MUNAKATA-EPC/Artemis_2023/Tournaments/2023_01_RoboChallenge/PresentationSeat/Pictures/Robo2.png

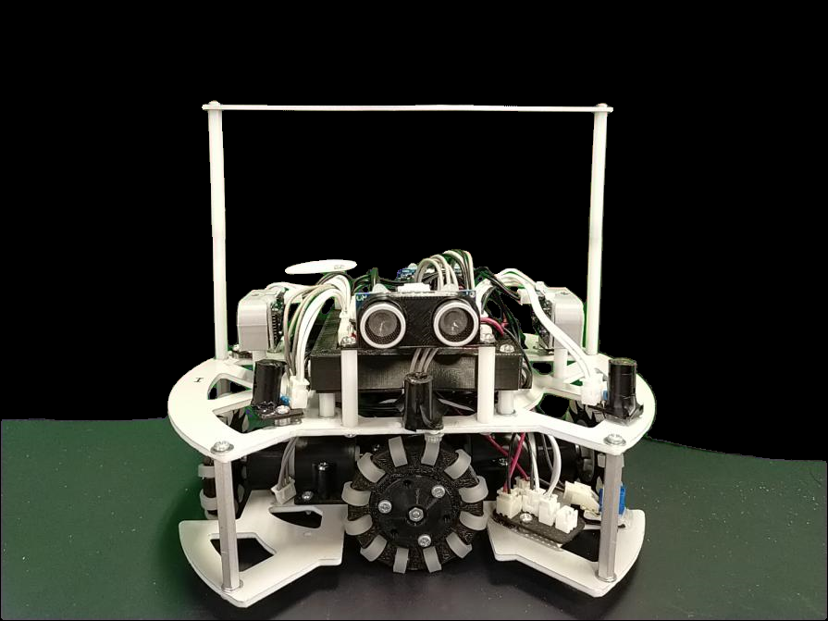
Tournaments/2023_01_RoboChallenge/PresentationSeat/Pictures/Robo2.png
