MUNAKATA-EPC/Artemis_2023/Design/2022 early/screw nut spacer/10mmスペーサー .png

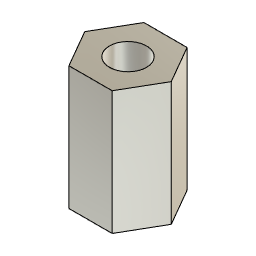
Design/2022 early/screw nut spacer/10mmスペーサー .png
