MUNAKATA-EPC/Artemis_2023/Design/2022 early/screw nut spacer/キャップボルト 8mm .png

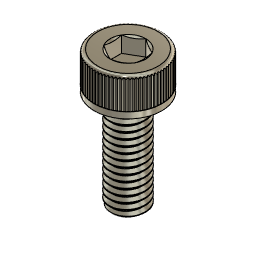
Design/2022 early/screw nut spacer/キャップボルト 8mm .png
