MUNAKATA-EPC/Artemis_2023/Design/artemis_pic/artemis.png

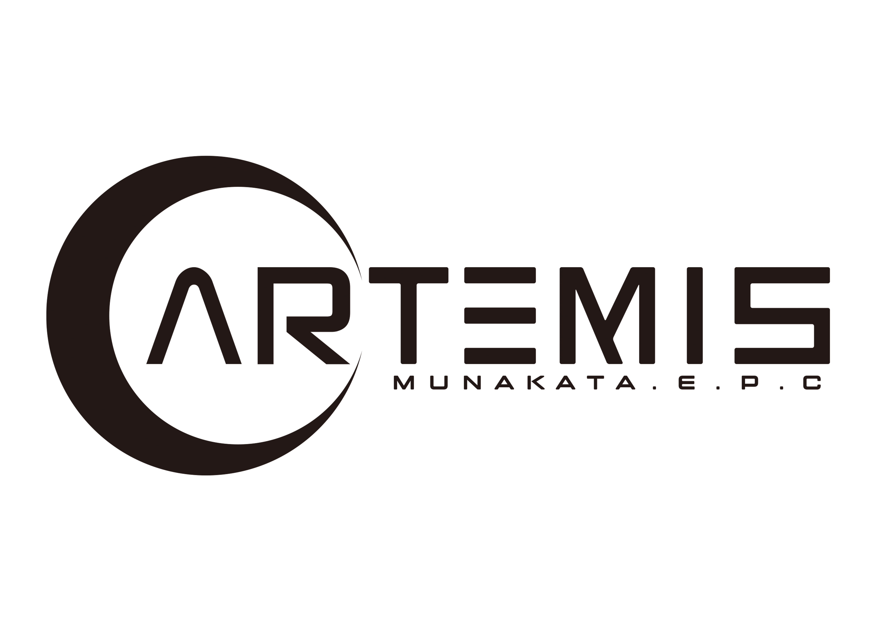
Design/artemis_pic/artemis.png
