MUNAKATA-EPC/Artemis_2023/Design/artemis_pic/artemis_text3.png

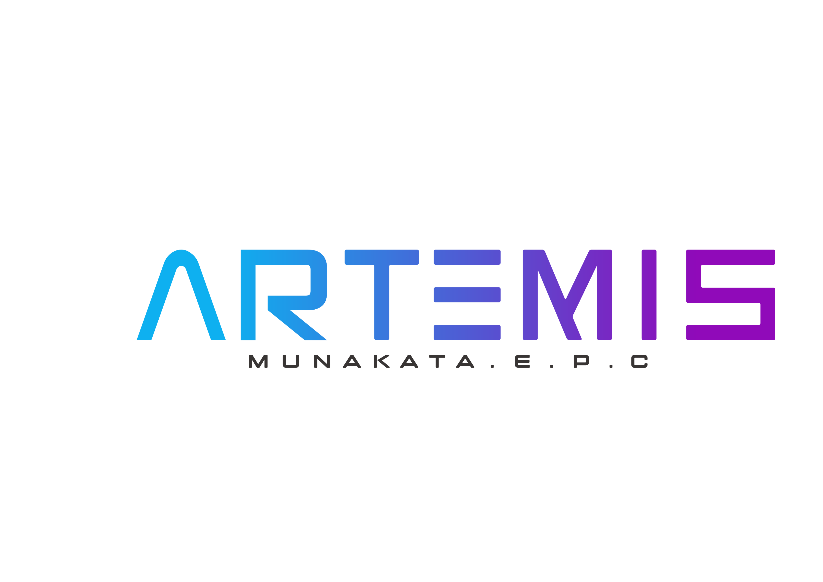
Design/artemis_pic/artemis_text3.png
