MUNAKATA-EPC/Artemis_2023/Design/artemis_pic/artemis_text.png

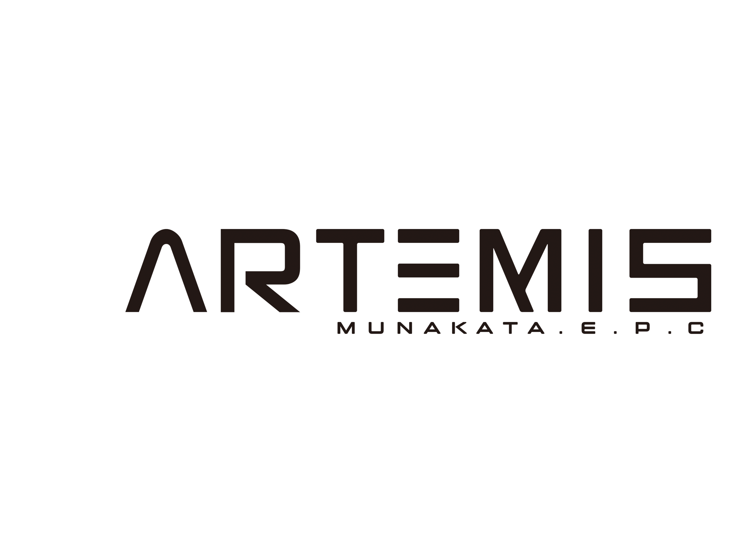
Design/artemis_pic/artemis_text.png
