MUNAKATA-EPC/Artemis_2023/Design/artemis_pic/moon2.png

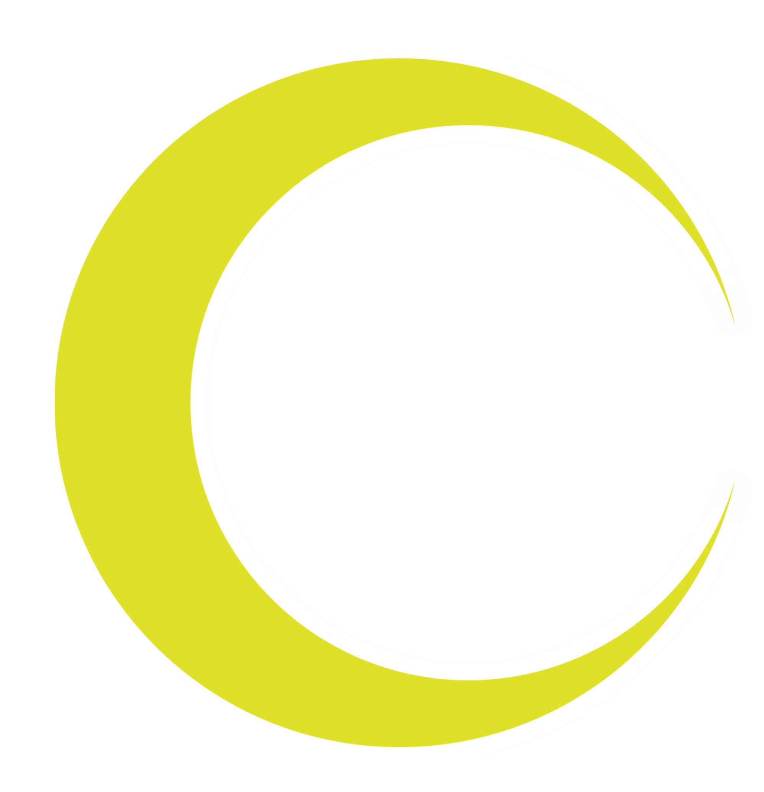
Design/artemis_pic/moon2.png
