MUNAKATA-EPC/Artemis_2023/Design/artemis_pic/moon_w.png

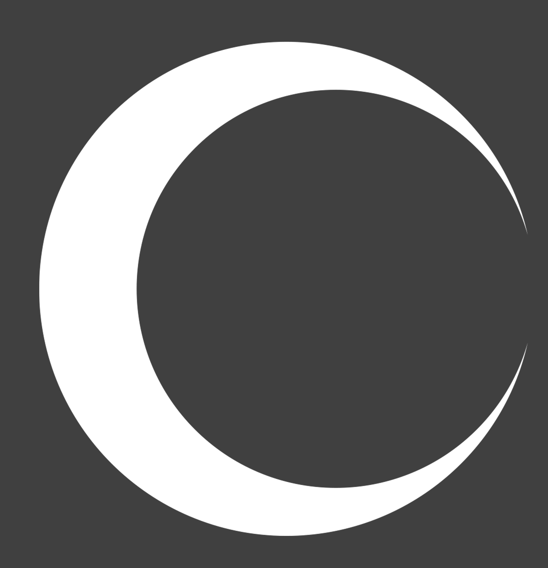
Design/artemis_pic/moon_w.png
