MUNAKATA-EPC/Artemis_2023/Tournaments/2023_00_KitakyusyuOpen/PresentationSeat/Pictures/JMP-BE-3561.png

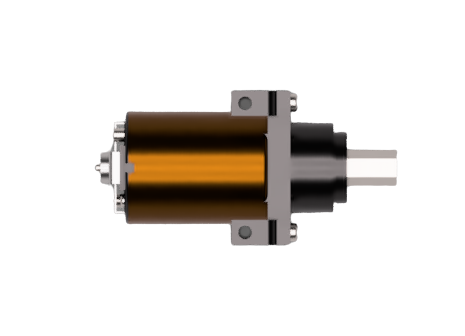
Tournaments/2023_00_KitakyusyuOpen/PresentationSeat/Pictures/JMP-BE-3561.png
