MUNAKATA-EPC/Artemis_2023/Tournaments/2023_00_KitakyusyuOpen/PresentationSeat/Pictures/Li-Po Battery.png

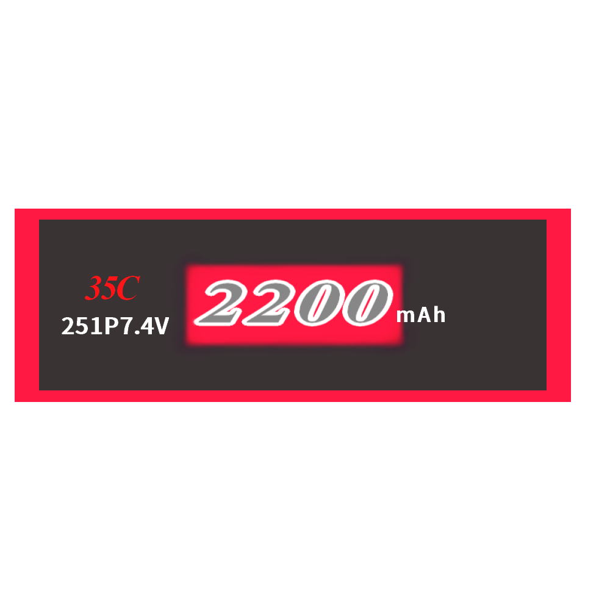
Tournaments/2023_00_KitakyusyuOpen/PresentationSeat/Pictures/Li-Po Battery.png
