MUNAKATA-EPC/Artemis_2023/Tournaments/2023_00_KitakyusyuOpen/PresentationSeat/Pictures/Motor.png

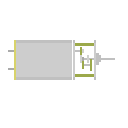
Tournaments/2023_00_KitakyusyuOpen/PresentationSeat/Pictures/Motor.png
