MUNAKATA-EPC/Artemis_2023/Tournaments/2023_00_KitakyusyuOpen/PresentationSeat/Pictures/Robo1.bmp

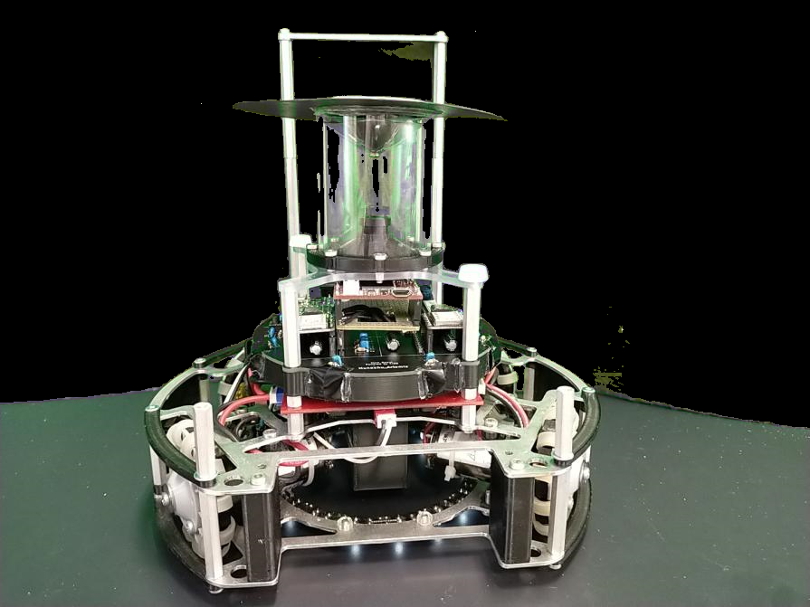
Tournaments/2023_00_KitakyusyuOpen/PresentationSeat/Pictures/Robo1.bmp
