MUNAKATA-EPC/Artemis_2023/Tournaments/2023_00_KitakyusyuOpen/PresentationSeat/Pictures/unknown.png

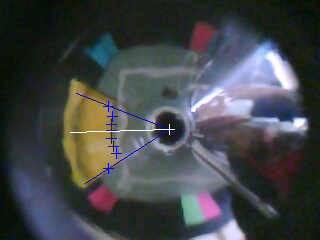
Tournaments/2023_00_KitakyusyuOpen/PresentationSeat/Pictures/unknown.png
