MUNAKATA-EPC/Artemis_2023/Tournaments/2023_04_JapanOpen/リチウムイオン二次電池資料/提出資料/WSL043_4.JPG

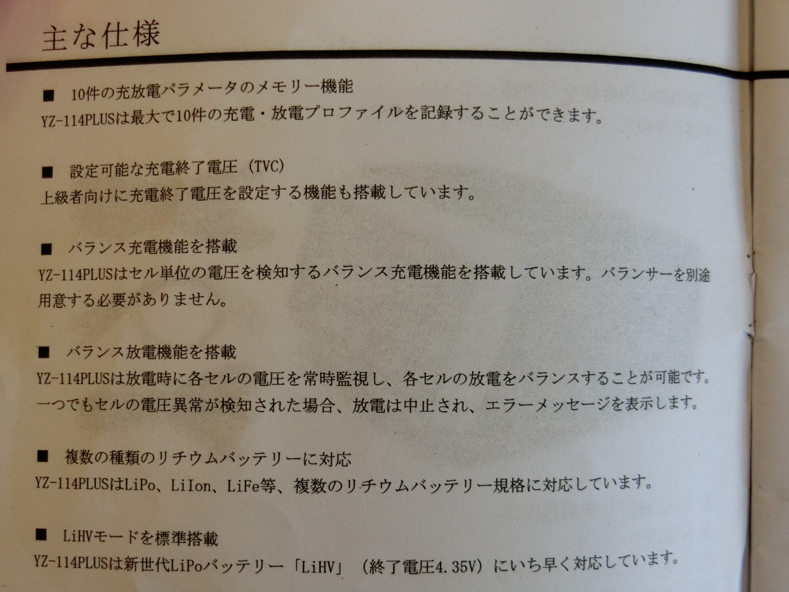
Tournaments/2023_04_JapanOpen/リチウムイオン二次電池資料/提出資料/WSL043_4.JPG
