MUNAKATA-EPC/Artemis_2023/Design/2022 late/ver.Teensy/3D printed components/筒固定具.stl

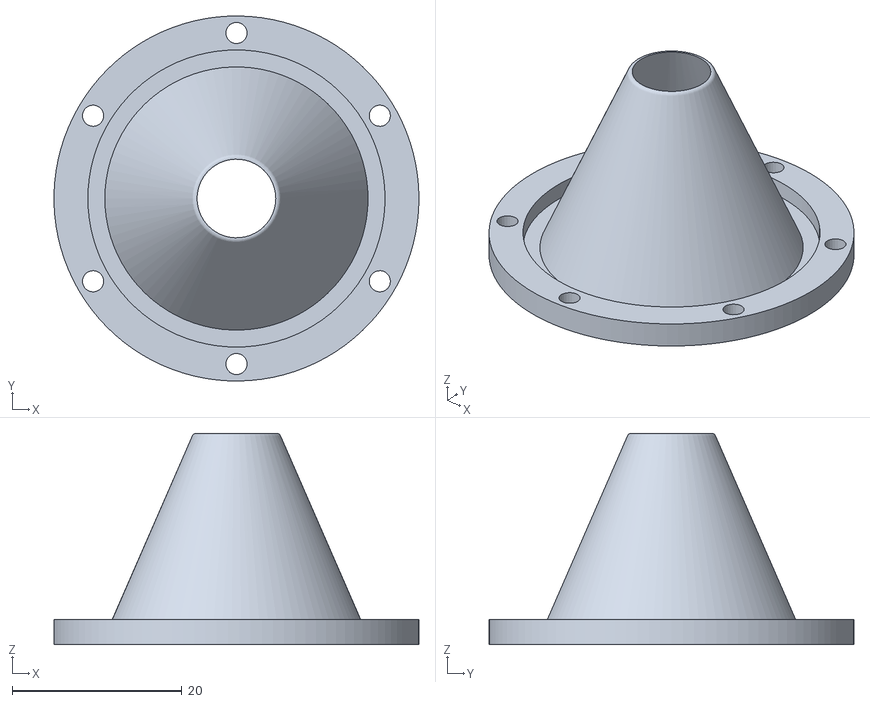
[picture p106: CAD file, 2022-12-09]
Design/2022 late/ver.Teensy/3D printed components/筒固定具.stl
43.0 x 43.0 x 24.9
