MUNAKATA-EPC/Artemis_2023/Design/2022 late/ver.Teensy/electric components/psu_board.step

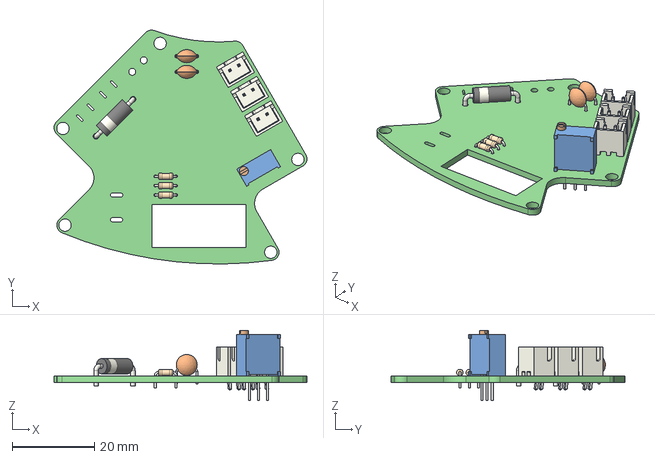
[picture p107: CAD file, 2022-12-09]
Design/2022 late/ver.Teensy/electric components/psu_board.step
61.5 x 56.9 x 17.1 mm
psu_board PCB
