MUNAKATA-EPC/Artemis_2023/Design/2022 late/ver.Teensy/jlcpcb_3dprinting/top_frame.stl

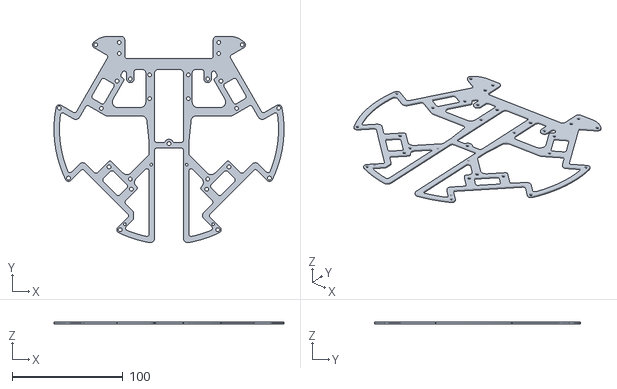
[picture p108: CAD file, 2022-12-09]
Design/2022 late/ver.Teensy/jlcpcb_3dprinting/top_frame.stl
207.9 x 186.5 x 1.50
