MUNAKATA-EPC/Artemis_2023/KiCad_Projects/3D_Data/2022 late/キッカー基板 v1.dxf

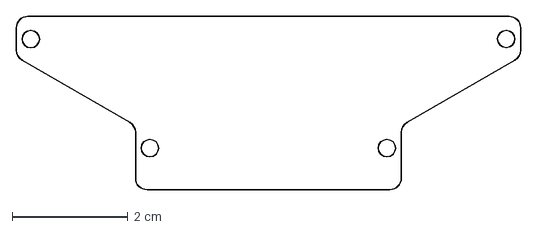
[picture p109: CAD file, 2022-12-09]
KiCad_Projects/3D_Data/2022 late/キッカー基板 v1.dxf
8.73 x 3.00 cm
