MUNAKATA-EPC/Artemis_2023/KiCad_Projects/3D_Data/2023 early/line統合.dxf

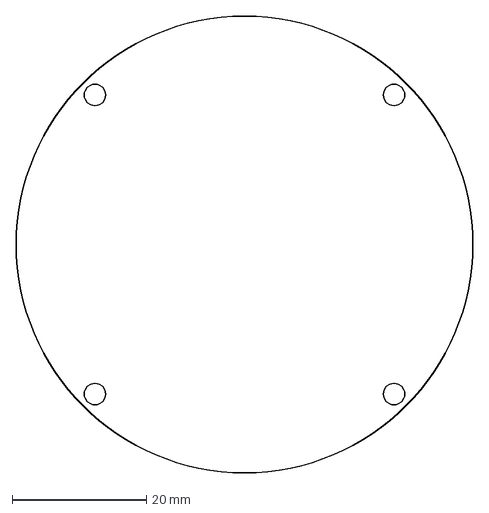
[picture p110: CAD file, 2023-03-06]
KiCad_Projects/3D_Data/2023 early/line統合.dxf
68.0 x 68.0 mm
