MUNAKATA-EPC/Artemis_2023/KiCad_Projects/3D_Data/ラインセンサー基板 .dxf

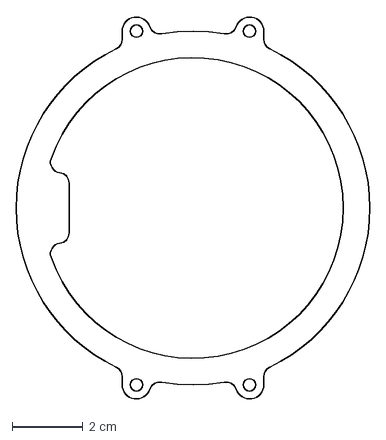
[picture p111: CAD file, 2022-06-29]
KiCad_Projects/3D_Data/ラインセンサー基板 .dxf
10.0 x 10.9 cm
