MUNAKATA-EPC/Artemis_2023/Design/2022 early/3D printed components/筒固定具.stl

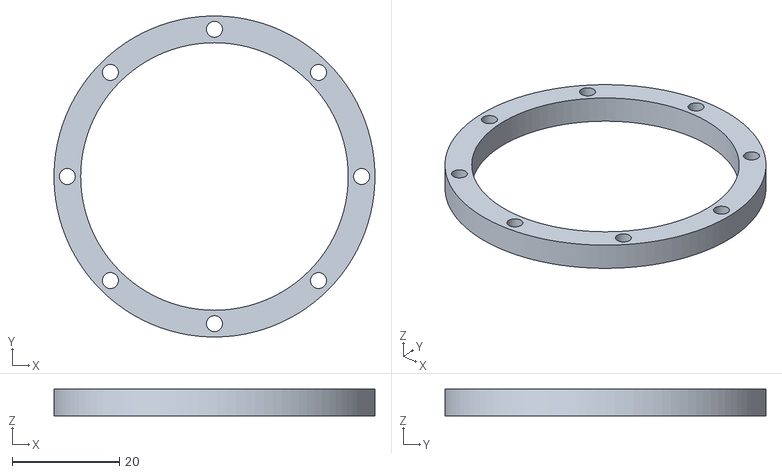
[picture p112: CAD file, 2022-07-31]
Design/2022 early/3D printed components/筒固定具.stl
60.0 x 60.0 x 5.00
