MUNAKATA-EPC/Artemis_2023/Design/2022 late/ver.Teensy/3D printed components/バッテリー固定具.stl

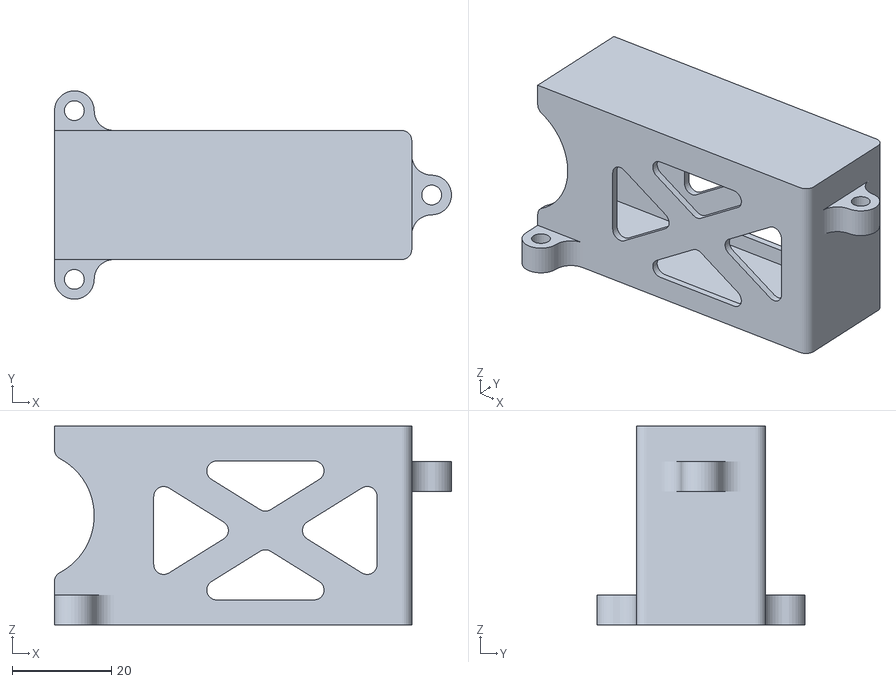
[picture p113: CAD file, 2022-12-09]
Design/2022 late/ver.Teensy/3D printed components/バッテリー固定具.stl
80.0 x 42.0 x 40.0
