MUNAKATA-EPC/Artemis_2023/Design/2022 late/ver.Teensy/electric components/kikker_PSU.step

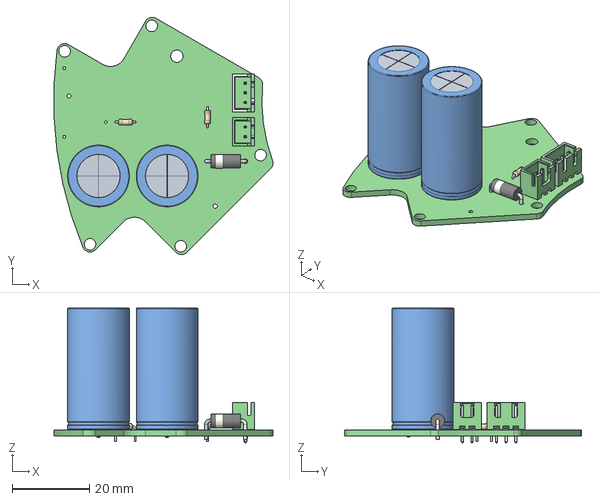
[picture p114: CAD file, 2022-12-09]
Design/2022 late/ver.Teensy/electric components/kikker_PSU.step
56.8 x 61.5 x 34.9 mm
kikker_PSU PCB
