MUNAKATA-EPC/Artemis_2023/Design/2022 late/ver.Teensy/jlcpcb_3dprinting/lower_frame.stl

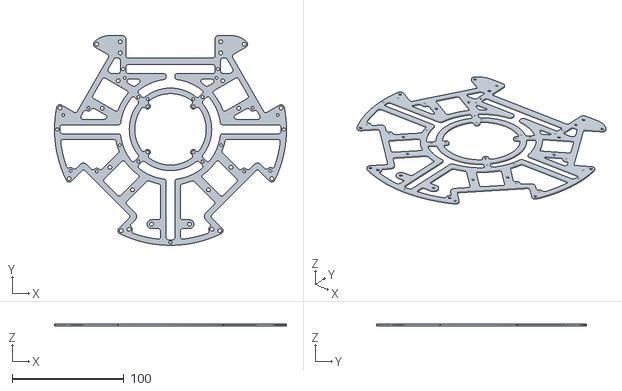
[picture p115: CAD file, 2022-12-09]
Design/2022 late/ver.Teensy/jlcpcb_3dprinting/lower_frame.stl
207.9 x 188.0 x 1.50
