MUNAKATA-EPC/Artemis_2023/KiCad_Projects/3D_Data/2022 late/IO基板 v4.dxf

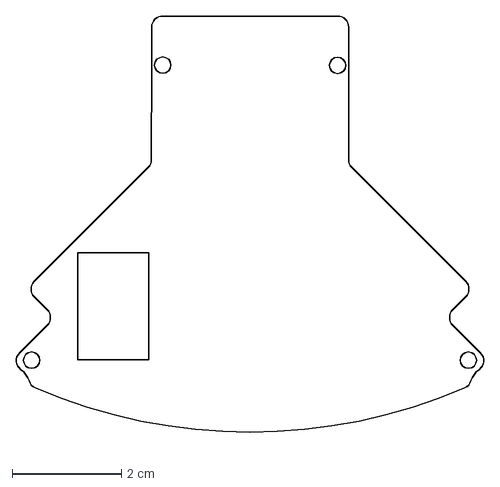
[picture p116: CAD file, 2022-10-13]
KiCad_Projects/3D_Data/2022 late/IO基板 v4.dxf
8.55 x 7.87 cm
