MUNAKATA-EPC/Artemis_2023/KiCad_Projects/3D_Data/IO基板 v1.dxf

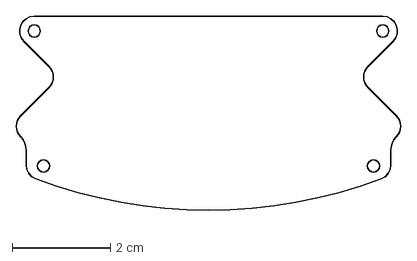
[picture p117: CAD file, 2022-06-24]
KiCad_Projects/3D_Data/IO基板 v1.dxf
7.84 x 4.17 cm
