MUNAKATA-EPC/Artemis_2023/Design/2022 early/3D printed components/バッテリーケース.stl

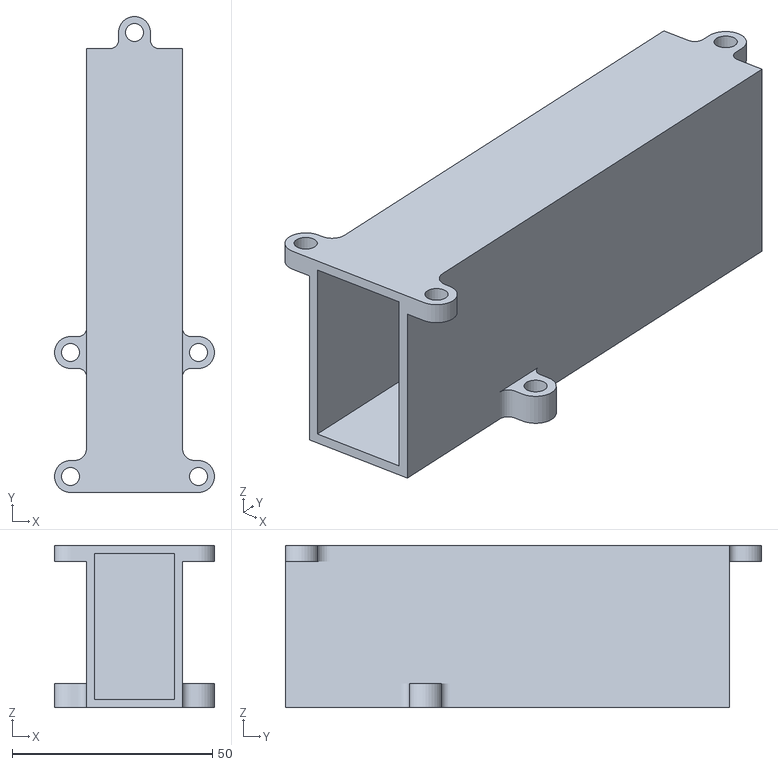
[picture p118: CAD file, 2022-07-31]
Design/2022 early/3D printed components/バッテリーケース.stl
40.0 x 119.0 x 40.5
