MUNAKATA-EPC/Artemis_2023/Design/2022 late/ver.Teensy/3D printed components/IR隠し.stl

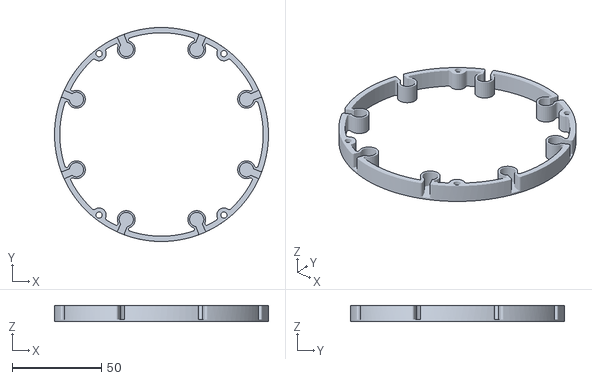
[picture p119: CAD file, 2022-12-09]
Design/2022 late/ver.Teensy/3D printed components/IR隠し.stl
120.0 x 120.0 x 9.00
