MUNAKATA-EPC/Artemis_2023/Design/2022 late/ver.Teensy/electric components/line 統合.step

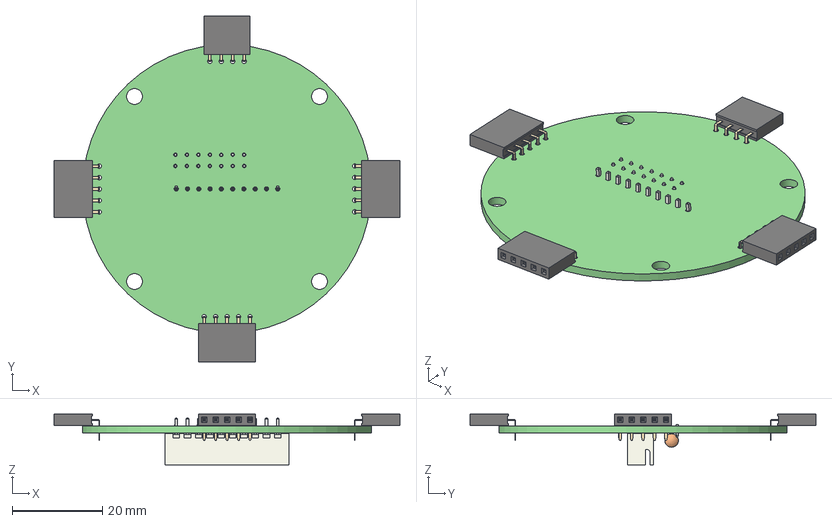
[picture p120: CAD file, 2022-10-13]
Design/2022 late/ver.Teensy/electric components/line 統合.step
76.7 x 76.7 x 11.2 mm
line çµ±å PCB
