MUNAKATA-EPC/Artemis_2023/Design/2022 early/3D printed components/IR隠し.stl

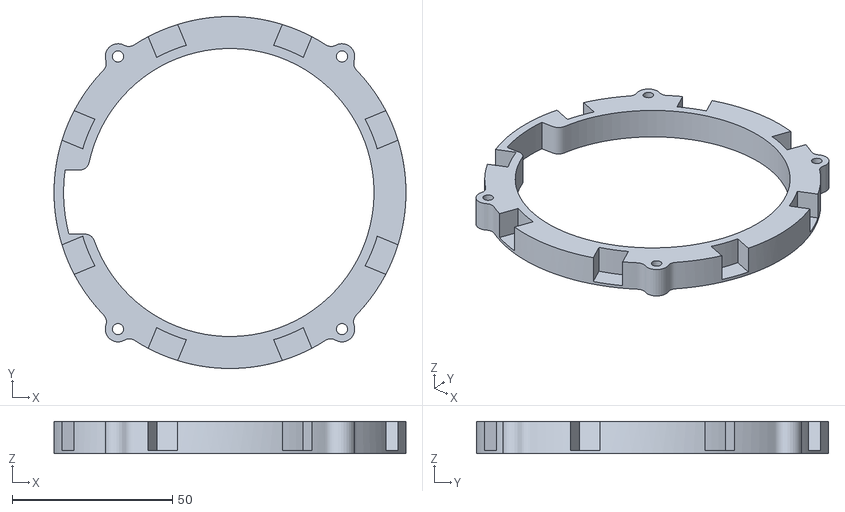
[picture p121: CAD file, 2022-07-31]
Design/2022 early/3D printed components/IR隠し.stl
110.0 x 110.0 x 10.0
