MUNAKATA-EPC/Artemis_2023/Design/2022 late/ver.Teensy/3D printed components/タッチセンサー v2.stl

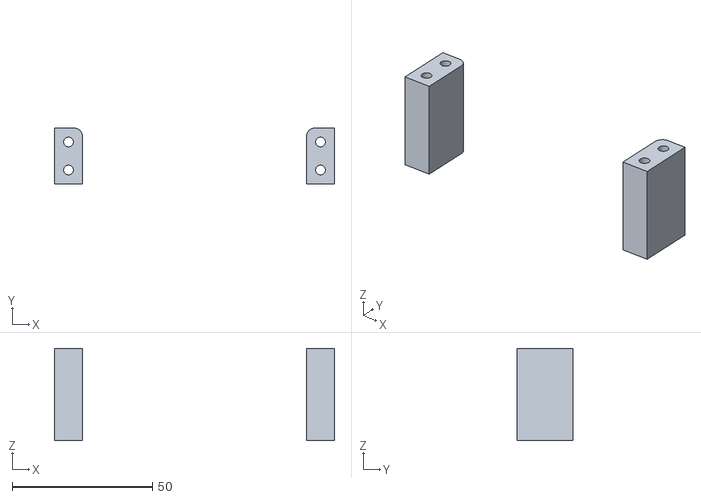
[picture p122: CAD file, 2022-12-09]
Design/2022 late/ver.Teensy/3D printed components/タッチセンサー v2.stl
100.0 x 20.0 x 33.0
