MUNAKATA-EPC/Artemis_2023/Design/2022 late/ver.Teensy/electric components/teensy4_header_breakout.step

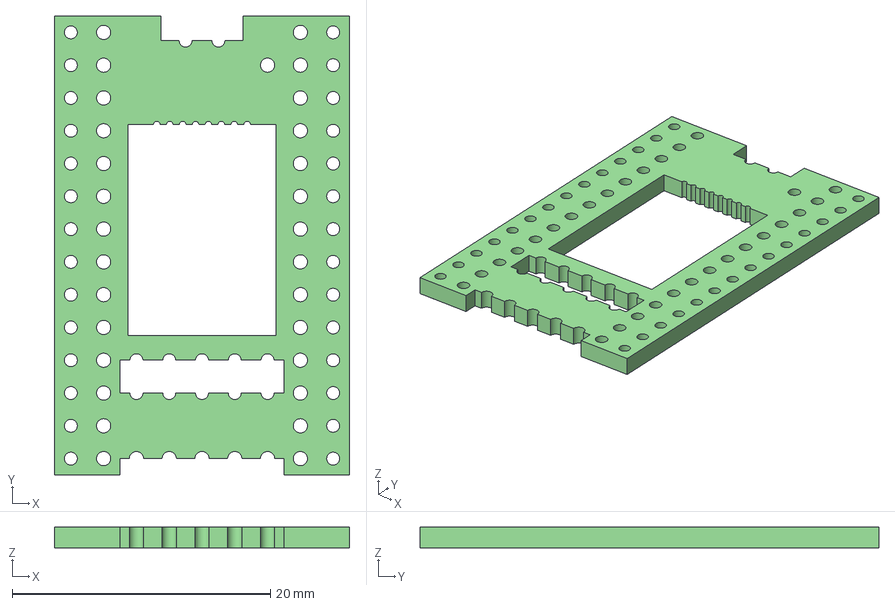
[picture p123: CAD file, 2022-10-13]
Design/2022 late/ver.Teensy/electric components/teensy4_header_breakout.step
22.9 x 35.6 x 1.60 mm
