MUNAKATA-EPC/Artemis_2023/Design/2022 late/ver.Teensy/jlcpcb_3dprinting/kikker_stay.stl

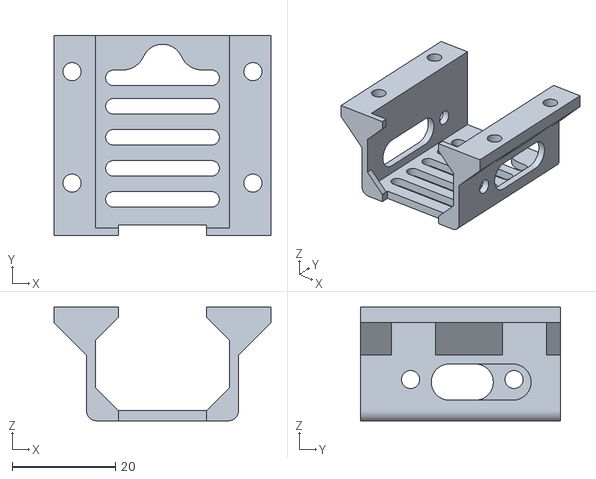
[picture p124: CAD file, 2022-12-09]
Design/2022 late/ver.Teensy/jlcpcb_3dprinting/kikker_stay.stl
42.0 x 38.7 x 22.0
