MUNAKATA-EPC/Artemis_2023/KiCad_Projects/3D_Data/2022 late/line統合.dxf

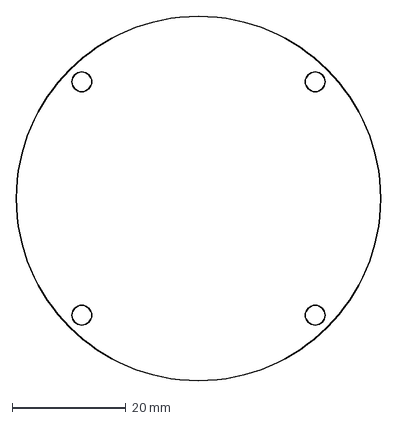
[picture p125: CAD file, 2022-10-13]
KiCad_Projects/3D_Data/2022 late/line統合.dxf
64.0 x 64.0 mm
