MUNAKATA-EPC/Artemis_2023/KiCad_Projects/3D_Data/基板 右 v3.dxf

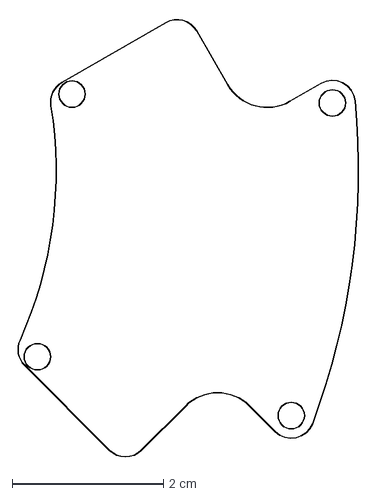
[picture p126: CAD file, 2022-06-22]
KiCad_Projects/3D_Data/基板 右 v3.dxf
4.62 x 5.83 cm
