MUNAKATA-EPC/Artemis_2023/Design/2022 late/ver.Teensy/3D printed components/5mm スペーサー v2.stl

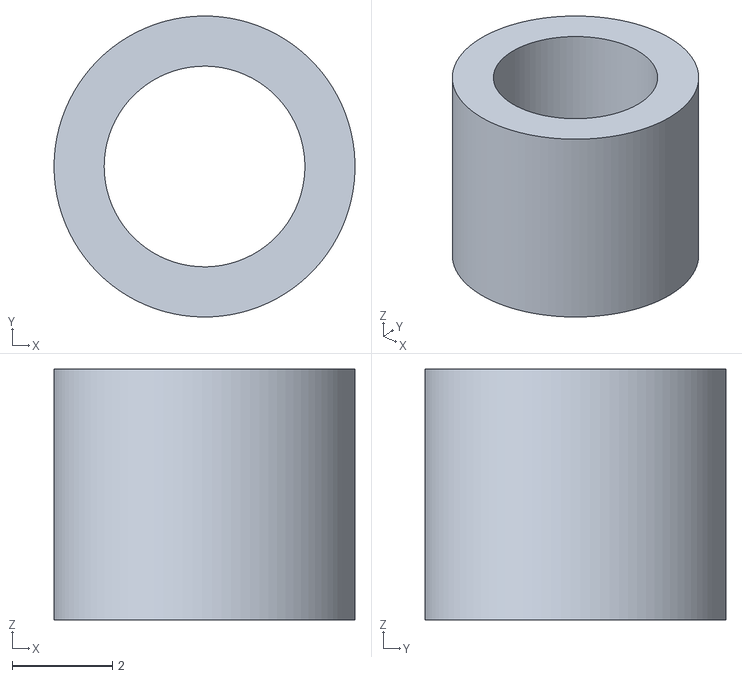
[picture p127: CAD file, 2022-12-09]
Design/2022 late/ver.Teensy/3D printed components/5mm スペーサー v2.stl
6.00 x 6.00 x 5.00
