MUNAKATA-EPC/Artemis_2023/Design/2022 late/ver.Teensy/electric components/line_sensor_right.step

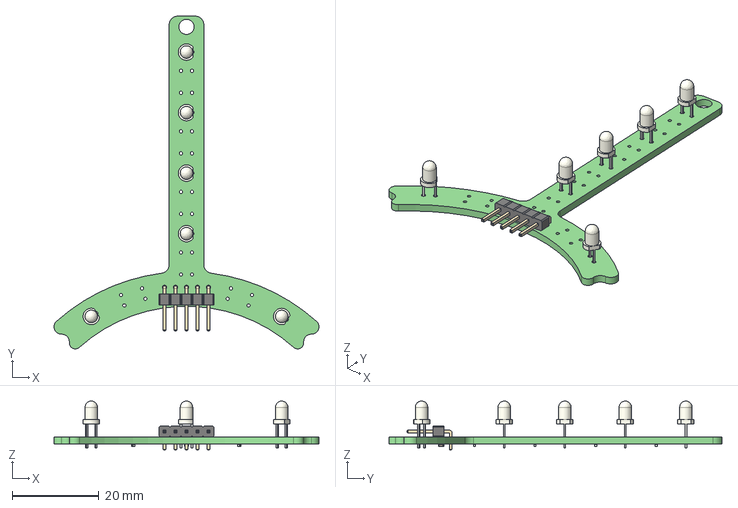
[picture p128: CAD file, 2022-10-13]
Design/2022 late/ver.Teensy/electric components/line_sensor_right.step
61.2 x 76.8 x 11.3 mm
line_sensor_right PCB
