MUNAKATA-EPC/Artemis_2023/Design/2022 late/ver.Teensy/jlcpcb_3dprinting/omni top.stl

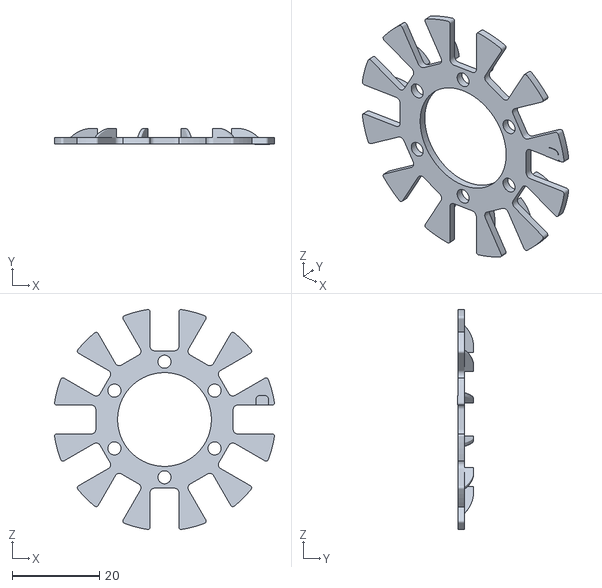
[picture p129: CAD file, 2022-07-31]
Design/2022 late/ver.Teensy/jlcpcb_3dprinting/omni top.stl
50.4 x 3.74 x 50.4
