MUNAKATA-EPC/Artemis_2023/KiCad_Projects/3D_Data/2022 late/ラインセンサー右.dxf

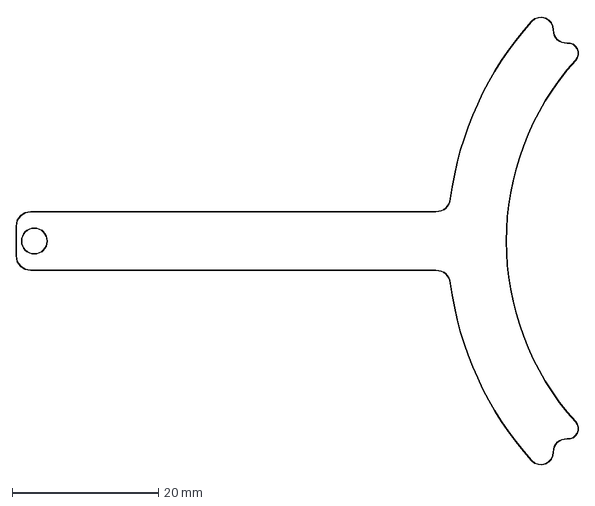
[picture p130: CAD file, 2022-10-13]
KiCad_Projects/3D_Data/2022 late/ラインセンサー右.dxf
76.9 x 61.4 mm
