MUNAKATA-EPC/Artemis_2023/Design/2022 late/ver.Teensy/electric components/line_sensor_front.step

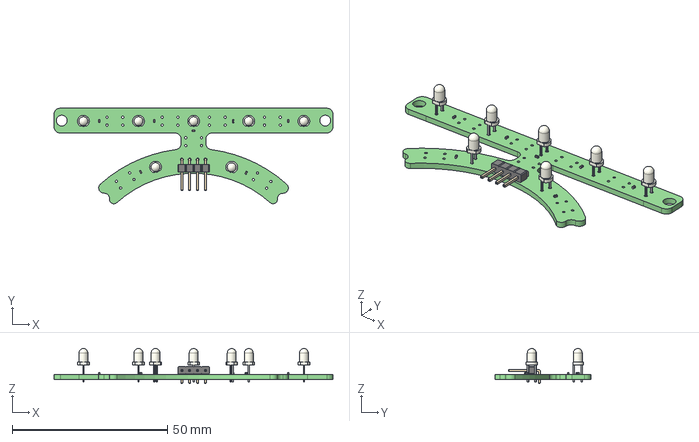
[picture p131: CAD file, 2022-10-13]
Design/2022 late/ver.Teensy/electric components/line_sensor_front.step
90.0 x 30.8 x 11.3 mm
line_sensor_front PCB
