MUNAKATA-EPC/Artemis_2023/Design/2022 late/ver.Teensy/jlcpcb_3dprinting/omuni stay.stl

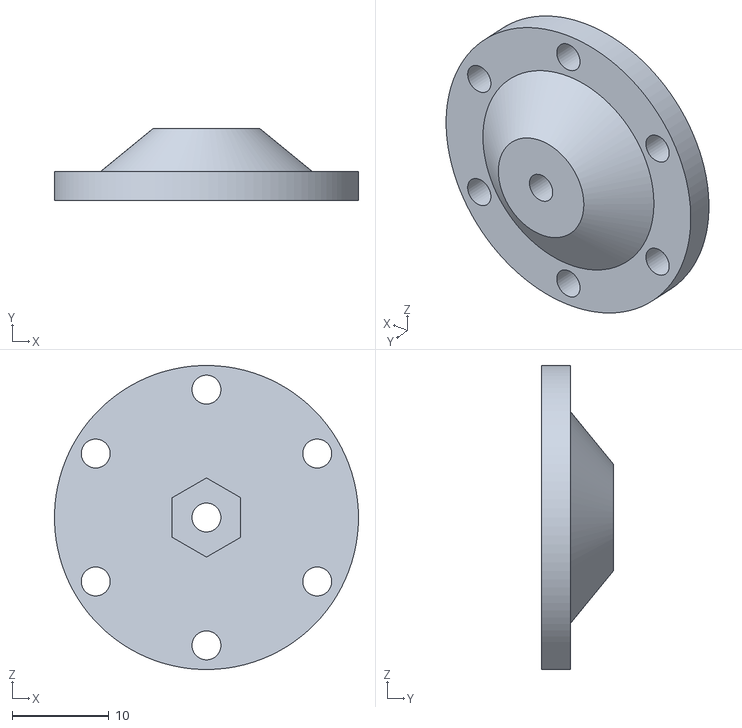
[picture p132: CAD file, 2022-06-01]
Design/2022 late/ver.Teensy/jlcpcb_3dprinting/omuni stay.stl
31.5 x 7.50 x 31.5
