MUNAKATA-EPC/Artemis_2023/KiCad_Projects/3D_Data/2022 late/基板左.dxf

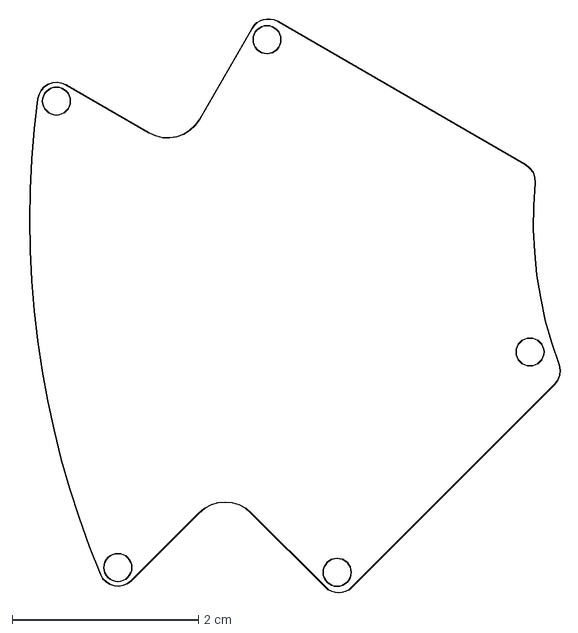
[picture p133: CAD file, 2022-10-13]
KiCad_Projects/3D_Data/2022 late/基板左.dxf
5.85 x 6.18 cm
