MUNAKATA-EPC/Artemis_2023/Design/2022 late/ver.Teensy/electric components/IO_Board.step

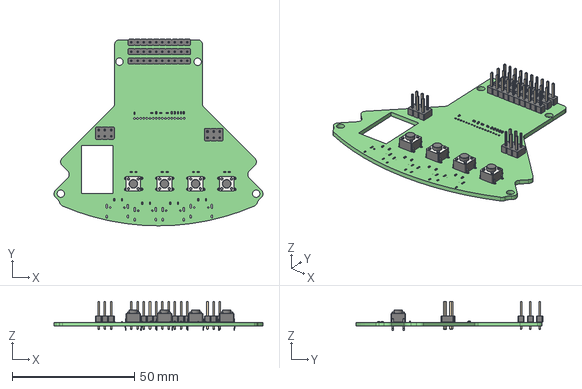
[picture p134: CAD file, 2022-10-13]
Design/2022 late/ver.Teensy/electric components/IO_Board.step
85.4 x 76.2 x 12.0 mm
IO_Board PCB
