MUNAKATA-EPC/Artemis_2023/Design/2022 late/ver.Teensy/jlcpcb_3dprinting/omni  lower.stl

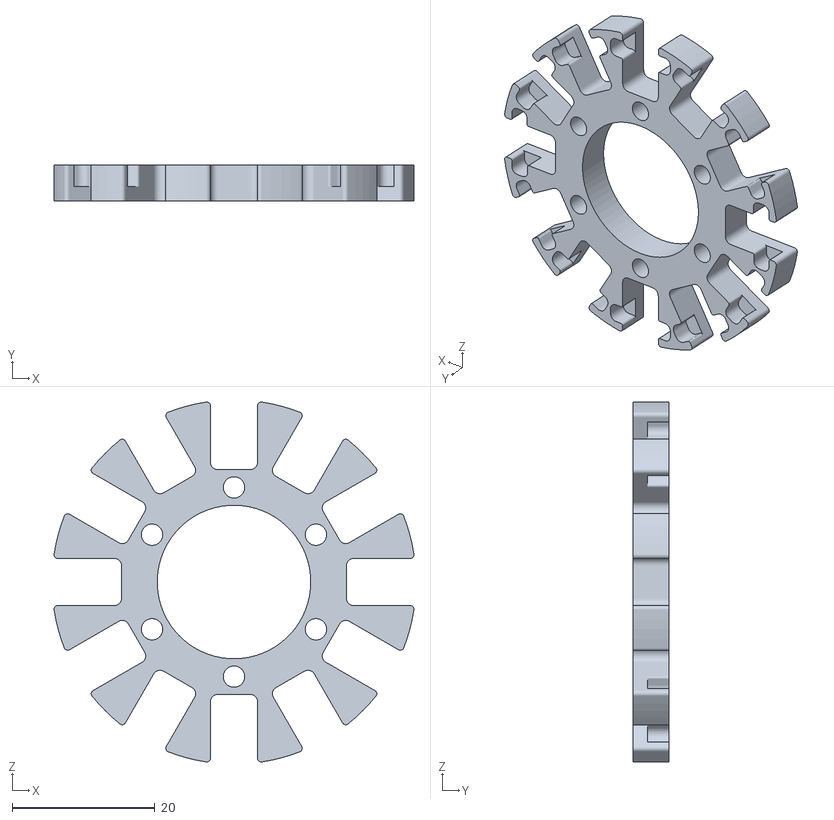
[picture p135: CAD file, 2022-06-01]
Design/2022 late/ver.Teensy/jlcpcb_3dprinting/omni lower.stl
50.4 x 5.00 x 50.4
