MUNAKATA-EPC/Artemis_2023/KiCad_Projects/3D_Data/2022 late/メイン基板 .dxf

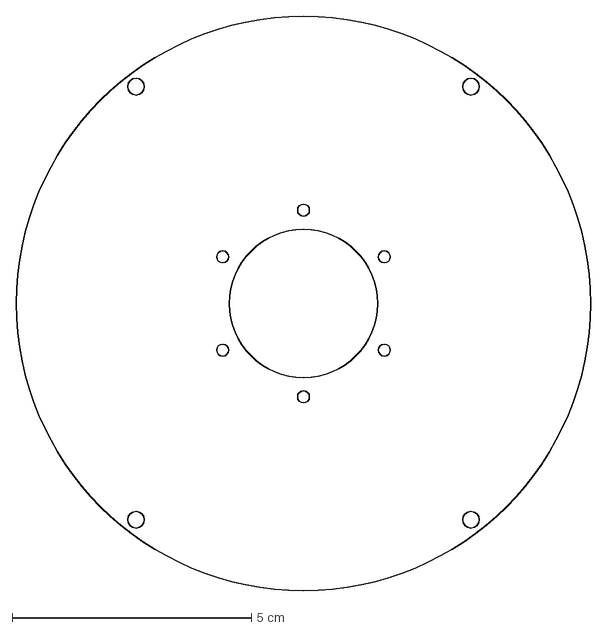
[picture p136: CAD file, 2022-10-13]
KiCad_Projects/3D_Data/2022 late/メイン基板 .dxf
12.0 x 12.0 cm
