MUNAKATA-EPC/Artemis_2023/KiCad_Projects/3D_Data/2022 late/ラインセンサー前 v1.dxf

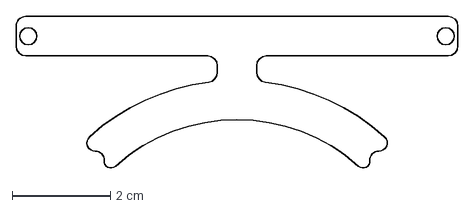
[picture p137: CAD file, 2022-10-13]
KiCad_Projects/3D_Data/2022 late/ラインセンサー前 v1.dxf
9.00 x 3.10 cm
