MUNAKATA-EPC/Artemis_2023/KiCad_Projects/その他/teensy4_header_breakout-master/teensy4_header_breakout-master/teensy4_header_breakout.kicad_pcb

## KiCad design KiCad_Projects/その他/teensy4_header_breakout-master/teensy4_header_breakout-master/teensy4_header_breakout.kicad_pcb (2022-10-13)

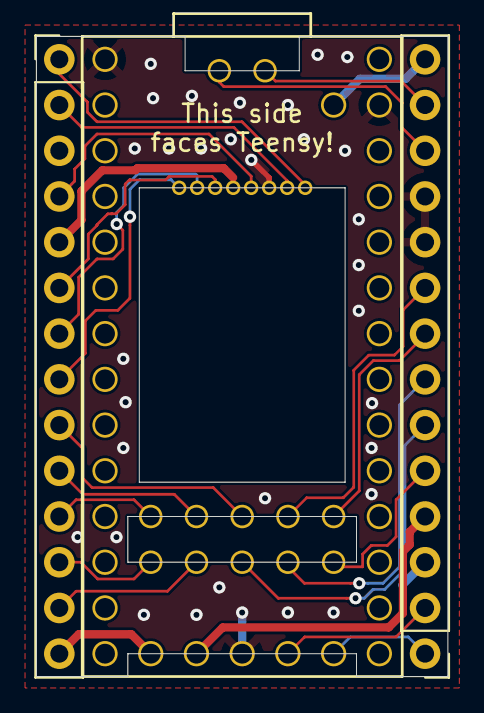
[picture p154: board teensy4_header_breakout.kicad_pcb from above]

Board: 2 copper layers, 22.9 x 35.6 mm, 3 parts (0 on the bottom side), 25 nets.

Parts:
J1, J2: Conn_01x14; PinHeader_1x14_P2.54mm_Vertical
U1: GND-1; Teensy40_SMT

Connections:
/3V3-1: J2.4, U1.16
/3V3-SD: J1.5, U1.49
/24: J2.5, U1.35
/25: J2.8, U1.36
/26: J2.7, U1.37
/27: J2.9, U1.38
/28: J2.6, U1.39
/29: J1.9, U1.40
/30: J1.13, U1.41
/31: J1.10, U1.42
/32: J1.12, U1.43
/33: J1.11, U1.44
/CLK: J1.4, U1.48
/CMD: J1.6, U1.50
/D+: J2.12, U1.54
/D-: J2.13, U1.53
/DAT0: J1.2, U1.46
/DAT1: J1.1, U1.45
/DAT2: J1.8, U1.52
/DAT3: J1.7, U1.51
/GND: J1.3, J2.3, J2.10, J2.11, U1.1, U1.17, U1.32, U1.47
/ON_OFF: J2.1, U1.19
/PROGRAM: J2.2, U1.18
/VBAT: J1.14, U1.15
/VUSB: J2.14, U1.34
