MUNAKATA-EPC/Artemis_2023/KiCad_Projects/2022 late/TJ3B_ver/main_board_TJ3B/main_board_TJ3B/main_board_TJ3B.kicad_pcb

## KiCad design KiCad_Projects/2022 late/TJ3B_ver/main_board_TJ3B/main_board_TJ3B/main_board_TJ3B.kicad_pcb (2023-03-06)

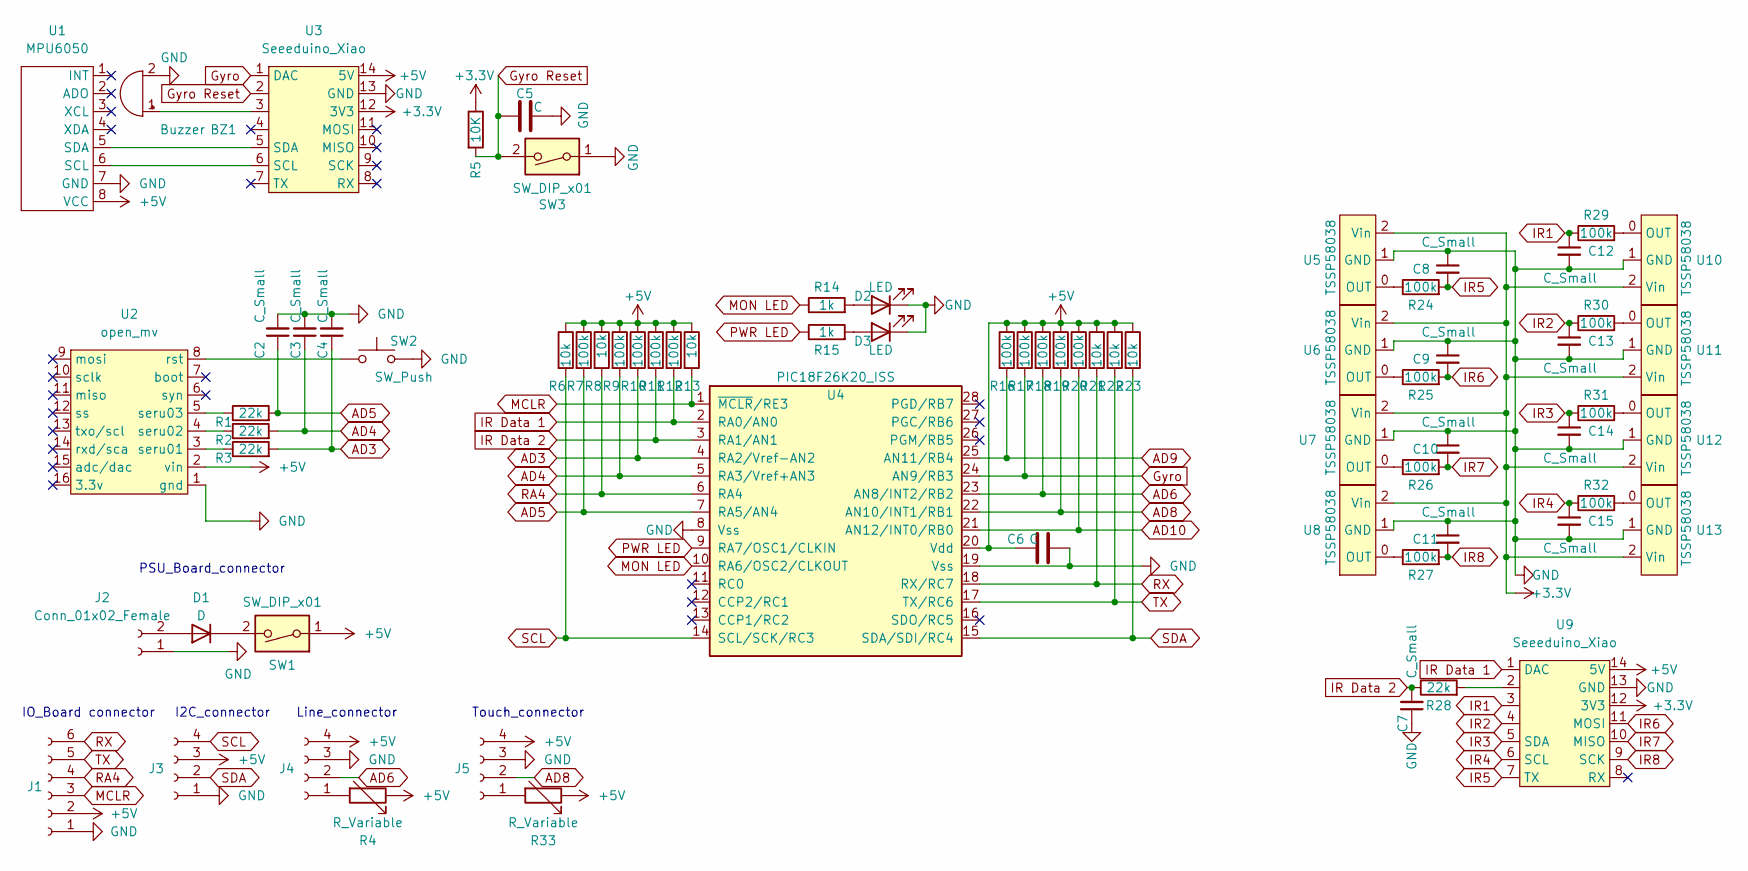
[picture p155: schematic main_board_TJ3B.kicad_sch]

Parts:
BZ1: Buzzer; Buzzer_12x9.5RM7.6
C2, C3, C4, C7: C_Small; C_0402_1005Metric; LCSC C528972
C5: C; C_0402_1005Metric; LCSC C507422
C6: C; CP_Radial_D5.0mm_P2.50mm
C8, C9, C10, C11, C12, C13, C14, C15: C_Small; C_0402_1005Metric; LCSC C507422
D1: D; D_DO-41_SOD81_P7.62mm_Horizontal
D2, D3: LED; LED_0402_1005Metric; LCSC C130725
J1: Conn_01x06_Female; JST_XH_B6B-XH-A_1x06_P2.50mm_Vertical
J2: Conn_01x02_Female; JST_XH_B2B-XH-A_1x02_P2.50mm_Vertical
J3, J4, J5: Conn_01x04_Female; JST_XH_B4B-XH-A_1x04_P2.50mm_Vertical
R1, R2, R3, R28: 22k; R_0402_1005Metric; LCSC C25768
R4, R33: R_Variable; 可変抵抗(小)
R5: 10K; R_0402_1005Metric; LCSC C269674
R6, R8, R13, R21, R22, R23: 10k; R_0402_1005Metric; LCSC C269674
R7, R9, R10, R11, R12, R16, R17, R18, R19, R20, R24, R25, R26, R27, R29, R30, R31, R32: 100k; R_0402_1005Metric; LCSC C269673
R14, R15: 1k; R_0402_1005Metric; LCSC C11702
SW1: SW_DIP_x01; 2MS1T2B4M2QES
SW2: SW_Push; SW_PUSH_6mm_H5mm
SW3: SW_DIP_x01; SW_PUSH_6mm_H5mm
U1: MPU6050
U2: open_mv; OpenMV
U3, U9: Seeeduino_Xiao; seeeduinoXIAO
U4: PIC18F26K20_ISS; DIP-28_W7.62mm_Socket
U5, U6, U7, U8, U10, U11, U12, U13: TSSP58038; TSSP58038_IR

Connections:
+3V3: R5.1, U3.12 (3V3), U5.2 (Vin), U6.2 (Vin), U7.2 (Vin), U8.2 (Vin), U9.12 (3V3), U10.2 (Vin), U11.2 (Vin), U12.2 (Vin), U13.2 (Vin)
+5V: C6.1, J1.2, J3.3, J4.4, J5.4, R4.1, R6.1, R7.1, R8.1, R9.1, R10.1, R11.1, R12.1, R13.1, R16.1, R17.1, R18.1, R19.1, R20.1, R21.1, R22.1, R23.1, R33.1, SW1.1, U1.8 (VCC), U2.2 (vin), U3.14 (5V), U4.20 (Vdd), U9.14 (5V)
AD3: C4.1, R3.2, R10.2, U4.4 (RA2/Vref-AN2)
AD4: C3.1, R2.2, R9.2, U4.5 (RA3/Vref+AN3)
AD5: C2.1, R1.2, R7.2, U4.7 (RA5/AN4)
AD6: J4.2, R18.2, U4.23 (AN8/INT2/RB2)
AD8: J5.2, R19.2, U4.22 (AN10/INT1/RB1)
AD9: R16.2, U4.25 (AN11/RB4)
AD10: R20.2, U4.21 (AN12/INT0/RB0)
GND: BZ1.2 (+), C2.2, C3.2, C4.2, C5.2, C6.2, C7.1, C8.1, C9.1, C10.1, C11.1, C12.2, C13.2, C14.2, C15.2, D2.1 (K), D3.1 (K), J1.1, J2.1, J3.1, J4.3, J5.3, SW2.2, SW3.1, U1.7 (GND), U2.1 (gnd), U3.13 (GND), U4.8 (Vss), U4.19 (Vss), U5.1 (GND), U6.1 (GND), U7.1 (GND), U8.1 (GND), U9.13 (GND), U10.1 (GND), U11.1 (GND), U12.1 (GND), U13.1 (GND)
Gyro: R17.2, U3.1 (DAC), U4.24 (AN9/RB3)
Gyro Reset: C5.1, R5.2, SW3.2, U3.2
IR1: C12.1, R29.1, U9.3
IR2: C13.1, R30.1, U9.4
IR3: C14.1, R31.1, U9.5 (SDA)
IR4: C15.1, R32.1, U9.6 (SCL)
IR5: C8.2, R24.2, U9.7 (TX)
IR6: C9.2, R25.2, U9.11 (MOSI)
IR7: C10.2, R26.2, U9.10 (MISO)
IR8: C11.2, R27.2, U9.9 (SCK)
IR Data 1: R12.2, U4.2 (RA0/AN0), U9.1 (DAC)
IR Data 2: C7.2, R11.2, R28.1, U4.3 (RA1/AN1)
MCLR: J1.3, R13.2, U4.1 (~MCLR/RE3)
MON LED: R14.1, U4.10 (RA6/OSC2/CLKOUT)
unnamed: BZ1.1 (-), U3.3
unnamed: D1.1 (K), SW1.2
unnamed: D1.2 (A), J2.2
unnamed: D2.2 (A), R14.2
unnamed: D3.2 (A), R15.2
unnamed: J4.1, R4.2
unnamed: J5.1, R33.2
unnamed: R1.1, U2.5 (seru03)
unnamed: R2.1, U2.4 (seru02)
unnamed: R3.1, U2.3 (seru01)
unnamed: R24.1, U5.0 (OUT)
unnamed: R25.1, U6.0 (OUT)
unnamed: R26.1, U7.0 (OUT)
unnamed: R27.1, U8.0 (OUT)
unnamed: R28.2, U9.2
unnamed: R29.2, U10.0 (OUT)
unnamed: R30.2, U11.0 (OUT)
unnamed: R31.2, U12.0 (OUT)
unnamed: R32.2, U13.0 (OUT)
unnamed: SW2.1, U2.8 (rst)
unnamed: U1.5 (SDA), U3.5 (SDA)
unnamed: U1.6 (SCL), U3.6 (SCL)
PWR LED: R15.1, U4.9 (RA7/OSC1/CLKIN)
RA4: J1.4, R8.2, U4.6 (RA4)
RX: J1.6, R21.2, U4.18 (RX/RC7)
SCL: J3.4, R6.2, U4.14 (SCL/SCK/RC3)
SDA: J3.2, R23.2, U4.15 (SDA/SDI/RC4)
TX: J1.5, R22.2, U4.17 (TX/RC6)

Notes on the sheet:
Touch_connector
PSU_Board_connector
Line_connector
I2C_connector
IO_Board connector

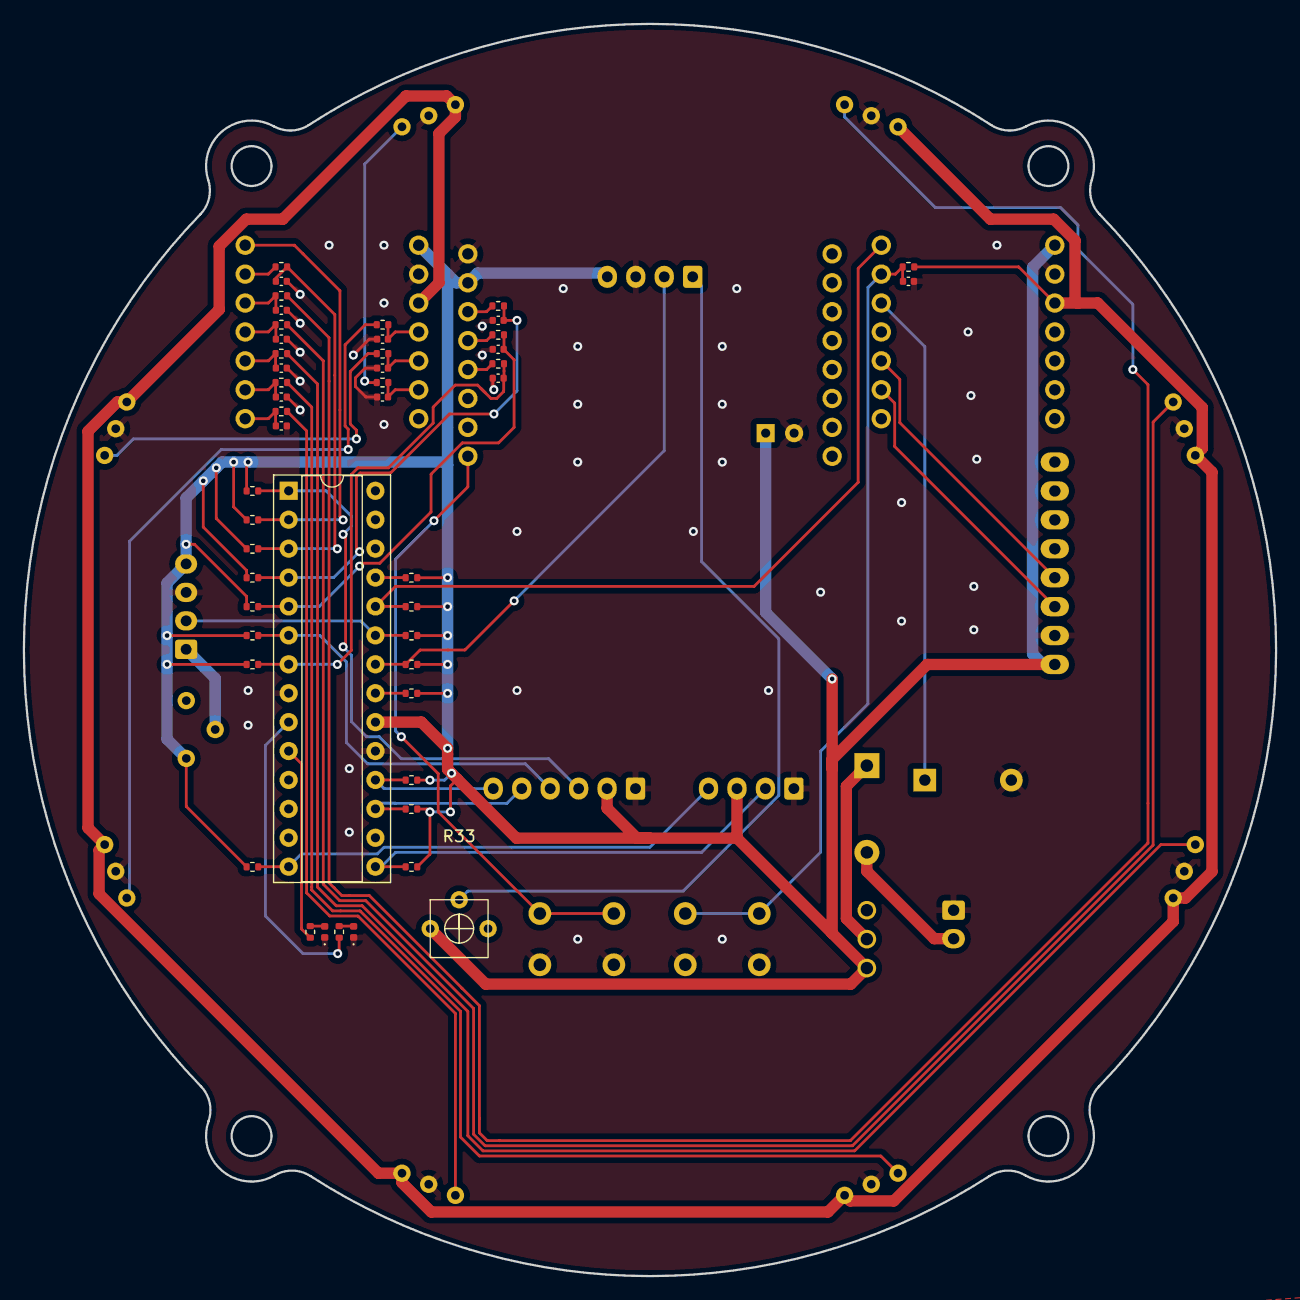
[picture p156: board main_board_TJ3B.kicad_pcb from above]

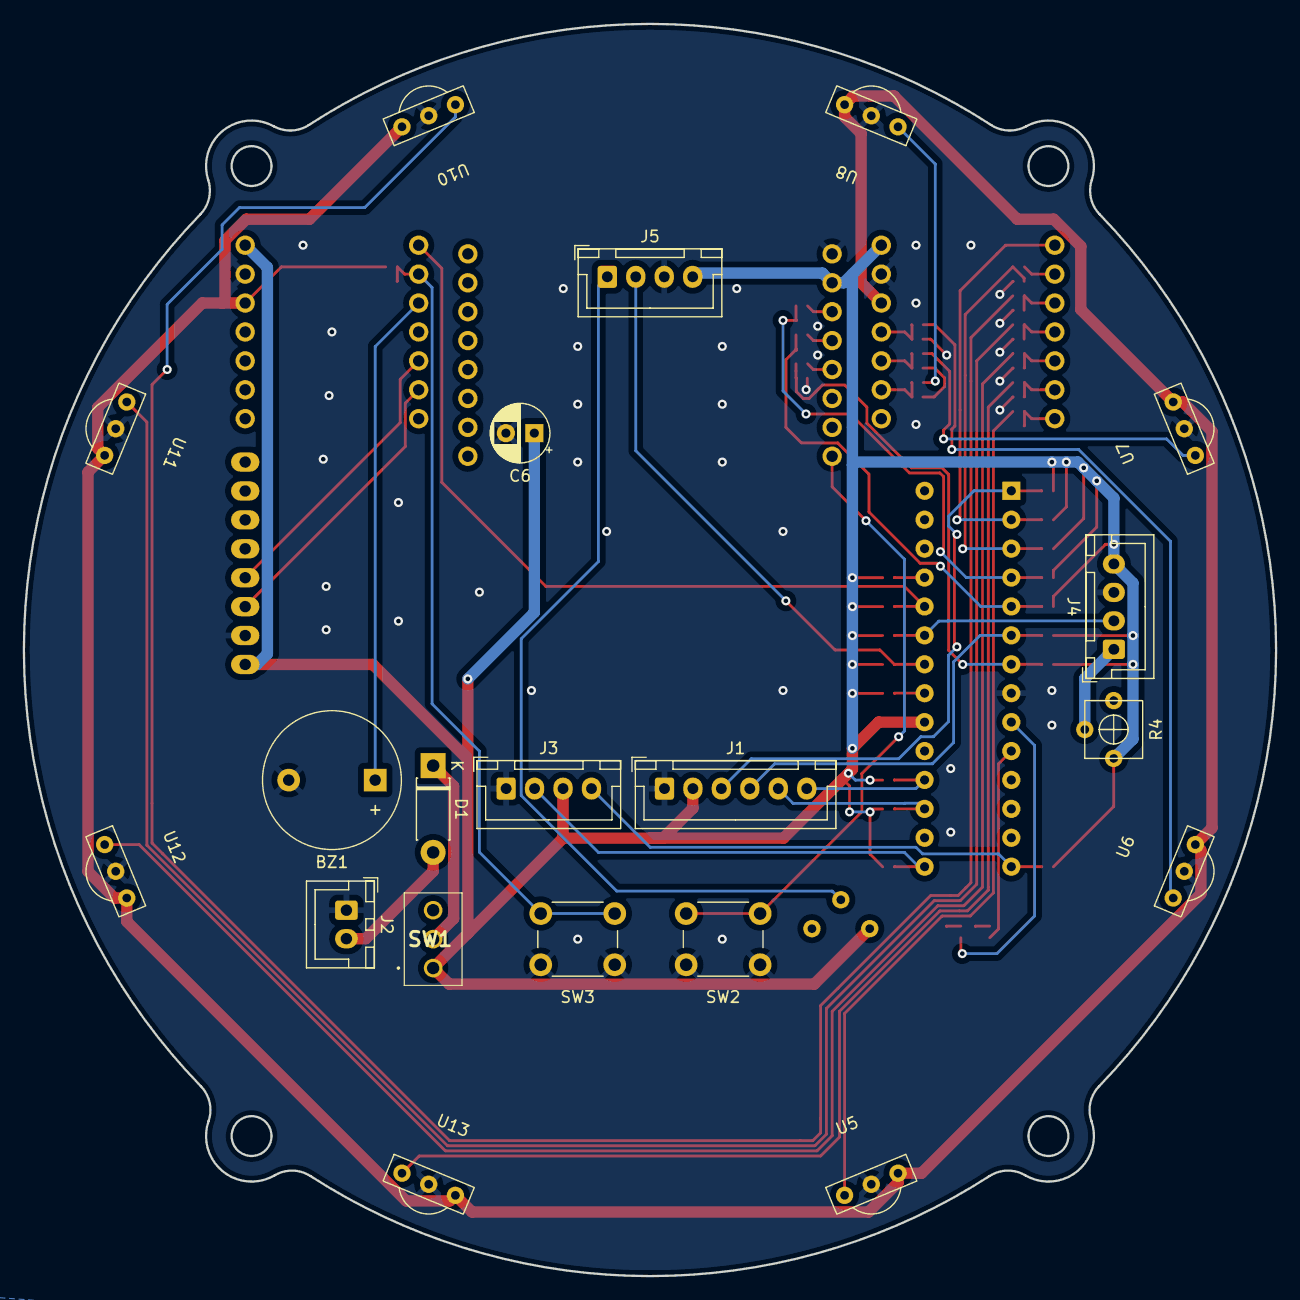
[picture p157: board main_board_TJ3B.kicad_pcb from below]

Board: 2 copper layers, 110.0 x 110.0 mm, 72 parts (21 on the bottom side), 52 nets.
