MUNAKATA-EPC/Artemis_2023/KiCad_Projects/その他/先輩の基板/USB-Serial/AT.kicad_pcb

## KiCad design KiCad_Projects/その他/先輩の基板/USB-Serial/AT.kicad_pcb (2022-10-13)

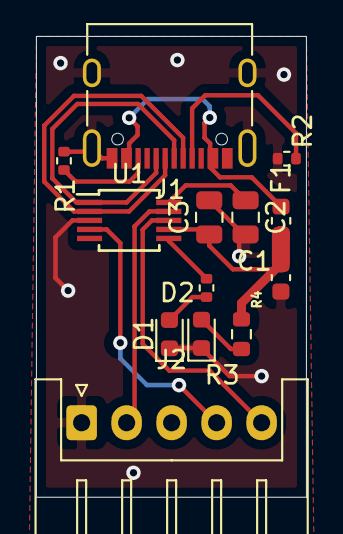
[picture p158: board KiCad_Projects/その他/先輩の基板/USB-Serial/AT.kicad_pcb from above]

Board: 2 copper layers, 15.0 x 25.6 mm, 13 parts (0 on the bottom side), 14 nets.

Parts:
C1: C_Small; C_0603_1608Metric
C2, C3: C_Small; C_0805_2012Metric
D1, D2: LED; LED_0603_1608Metric
F1: Fuse; Fuse_0603_1608Metric
J1: USB_C_Receptacle_USB2.0; USB_C_Receptacle_XKB_U262-16XN-4BVC11
J2: Conn_01x05; JST_XH_S5B-XH-A_1x05_P2.50mm_Horizontal
R1, R2, R4: R; R_0402_1005Metric
R3: R; R_0603_1608Metric
U1: CH340E; MSOP-10_3x3mm_P0.5mm

Connections:
GND: C1.2, C2.2, C3.2, D1.1, D2.1, J1.A1, J1.A12, J1.B1, J1.B12, J1.S1, J2.1, R1.1, R2.1, U1.3
unnamed: C2.1, U1.10
unnamed: D1.2, R4.2
unnamed: D2.2, R3.1
unnamed: F1.2, J1.A4, J1.A9, J1.B4, J1.B9
unnamed: J1.A5, R2.2
unnamed: J1.A6, J1.B6, U1.1
unnamed: J1.A7, J1.B7, U1.2
unnamed: J1.B5, R1.2
unnamed: J2.2, U1.9
unnamed: J2.4, U1.4
unnamed: J2.5, U1.8
unnamed: R4.1, U1.6
VCC: C1.1, C3.1, F1.1, R3.2, U1.7
