MUNAKATA-EPC/Artemis_2023/KiCad_Projects/その他/tj3b/tj3b core/TJ3B片面用/TJ3B.kicad_pcb

## KiCad design KiCad_Projects/その他/tj3b/tj3b core/TJ3B片面用/TJ3B.kicad_pcb (2022-06-01)

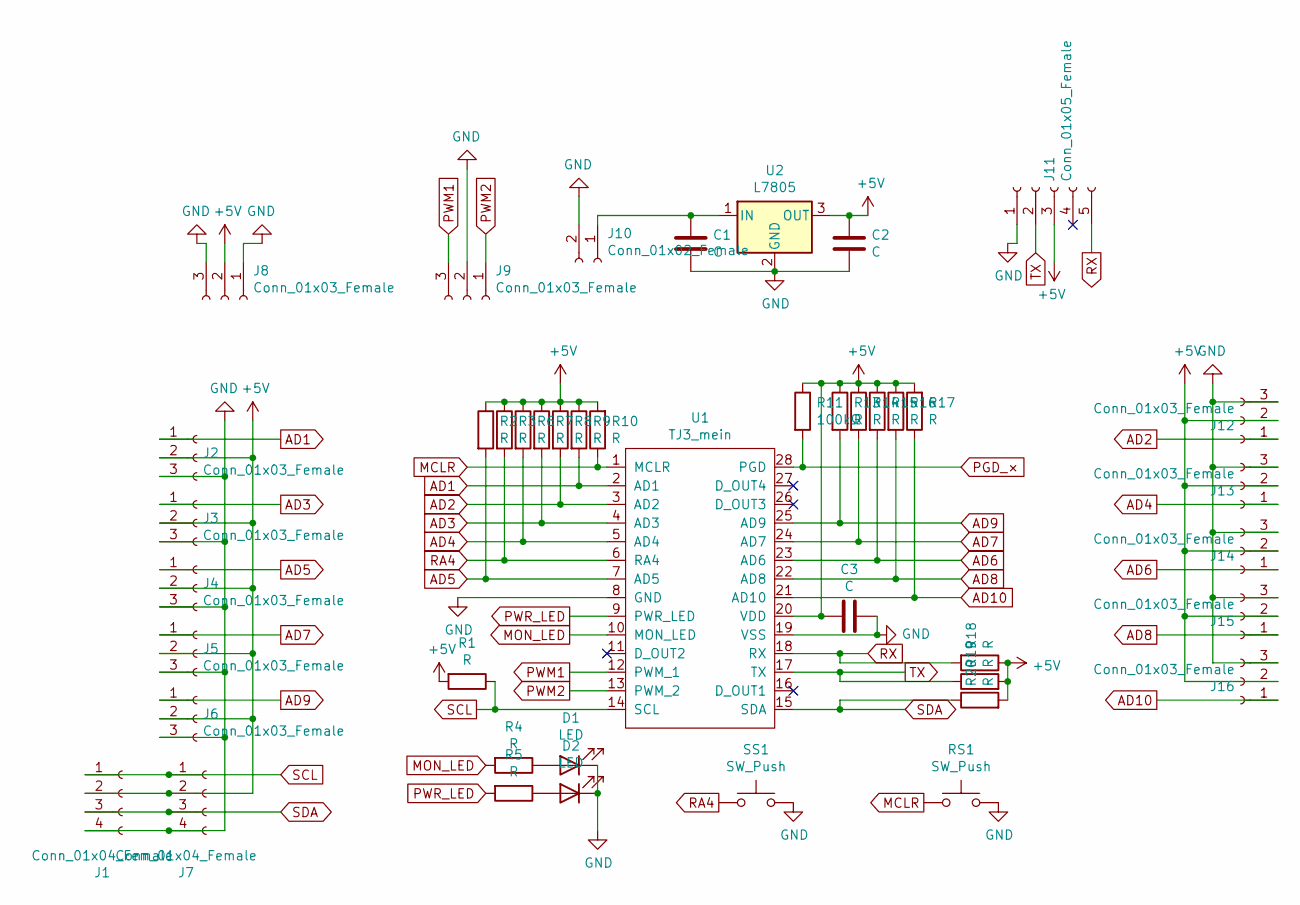
[picture p159: schematic TJ3B.sch]

Parts:
C1, C3: C; C_Disc_D3.0mm_W1.6mm_P2.50mm
C2: C; CP_Radial_D5.0mm_P2.00mm
D1, D2: LED; LED_D3.0mm
J1, J7: Conn_01x04_Female; JST_XH_B4B-XH-A_1x04_P2.50mm_Vertical
J2, J3, J4, J5, J6, J8, J9, J12, J13, J14, J15, J16: Conn_01x03_Female; JST_XH_B3B-XH-A_1x03_P2.50mm_Vertical
J10: Conn_01x02_Female; JST_XH_B2B-XH-A_1x02_P2.50mm_Vertical
J11: Conn_01x05_Female; JST_XH_B5B-XH-A_1x05_P2.50mm_Vertical
R1, R2, R3, R4, R5, R6, R7, R8, R9, R10, R13, R14, R15, R16, R17, R18, R19, R20: R; R_Axial_DIN0204_L3.6mm_D1.6mm_P5.08mm_Horizontal
R11: 100kΩ; R_Axial_DIN0204_L3.6mm_D1.6mm_P5.08mm_Horizontal
RS1: SW_Push; SW_PUSH_6mm
SS1: SW_Push; SW_PUSH_6mm
U1: TJ3_mein; DIP-28_W7.62mm_Socket
U2: L7805; TO-220-3_Vertical

Connections:
+5V: C2.1, C3.2, J1.2, J2.2, J3.2, J4.2, J5.2, J6.2, J7.2, J8.2, J11.3, J12.2, J13.2, J14.2, J15.2, J16.2, R1.2, R2.1, R3.1, R6.1, R7.1, R8.1, R9.1, R10.2, R11.1, R13.1, R14.1, R15.1, R16.1, R17.2, R18.1, R19.2, R20.2, U1.20 (VDD), U2.3 (OUT)
AD1: J2.1, R9.2, U1.2 (AD1)
AD2: J12.1, R8.2, U1.3 (AD2)
AD3: J3.1, R7.2, U1.4 (AD3)
AD4: J13.1, R6.2, U1.5 (AD4)
AD5: J4.1, R2.2, U1.7 (AD5)
AD6: J14.1, R15.2, U1.23 (AD6)
AD7: J5.1, R14.2, U1.24 (AD7)
AD8: J15.1, R16.2, U1.22 (AD8)
AD9: J6.1, R13.2, U1.25 (AD9)
AD10: J16.1, R17.1, U1.21 (AD10)
GND: C1.2, C2.2, C3.1, D1.1 (K), D2.1 (K), J1.4, J2.3, J3.3, J4.3, J5.3, J6.3, J7.4, J8.1, J8.3, J9.2, J10.2, J11.1, J12.3, J13.3, J14.3, J15.3, J16.3, RS1.2, SS1.2, U1.8 (GND), U1.19 (VSS), U2.2 (GND)
MCLR: R10.1, RS1.1, U1.1 (MCLR)
MON_LED: R4.2, U1.10 (MON_LED)
unnamed: C1.1, J10.1, U2.1 (IN)
unnamed: D1.2 (A), R4.1
unnamed: D2.2 (A), R5.1
PGD_×: R11.2, U1.28 (PGD)
PWM1: J9.3, U1.12 (PWM_1)
PWM2: J9.1, U1.13 (PWM_2)
PWR_LED: R5.2, U1.9 (PWR_LED)
RA4: R3.2, SS1.1, U1.6 (RA4)
RX: J11.5, R18.2, U1.18 (RX)
SCL: J1.1, J7.1, R1.1, U1.14 (SCL)
SDA: J1.3, J7.3, R20.1, U1.15 (SDA)
TX: J11.2, R19.1, U1.17 (TX)

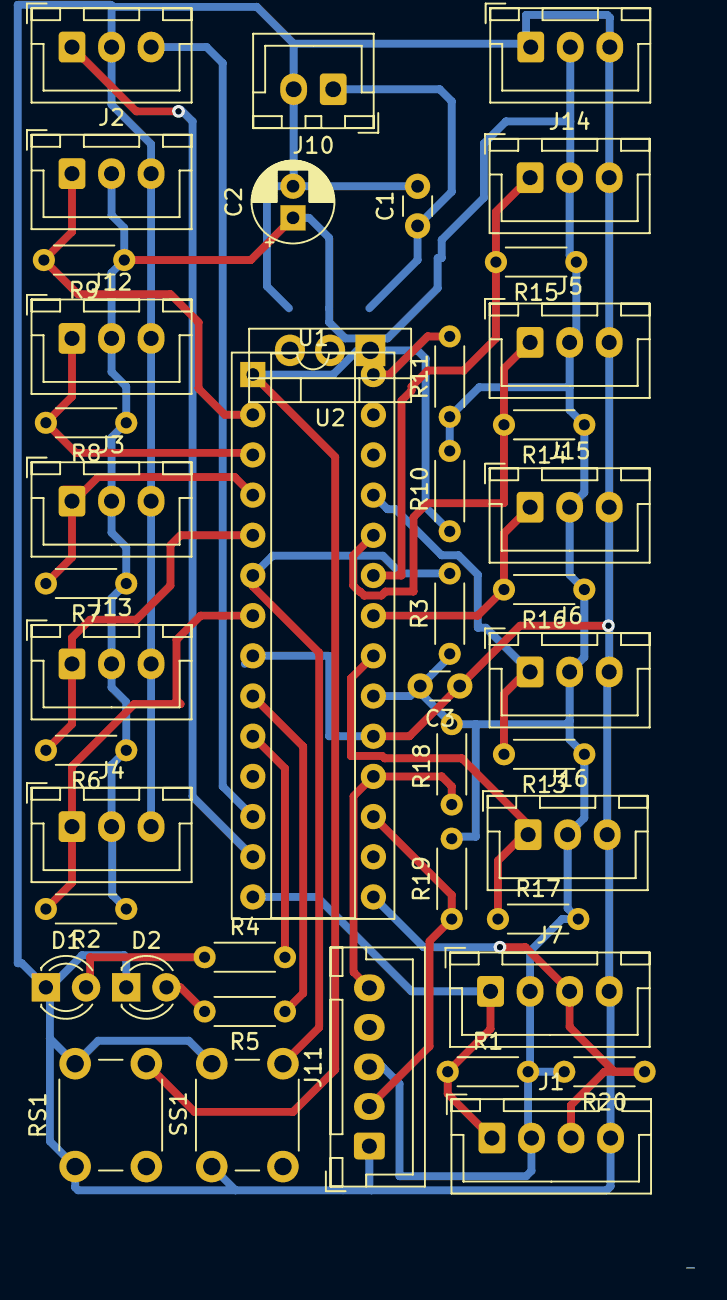
[picture p160: board KiCad_Projects/その他/tj3b/tj3b core/TJ3B片面用/TJ3B.kicad_pcb from above]

Board: 2 copper layers, 44 parts (0 on the bottom side), 26 nets.
