MUNAKATA-EPC/Artemis_2023/KiCad_Projects/2023 early/Teensy_ver/line_sensor/line 統合/line 統合.kicad_pcb

## KiCad design KiCad_Projects/2023 early/Teensy_ver/line_sensor/line 統合/line 統合.kicad_pcb (2022-10-13)

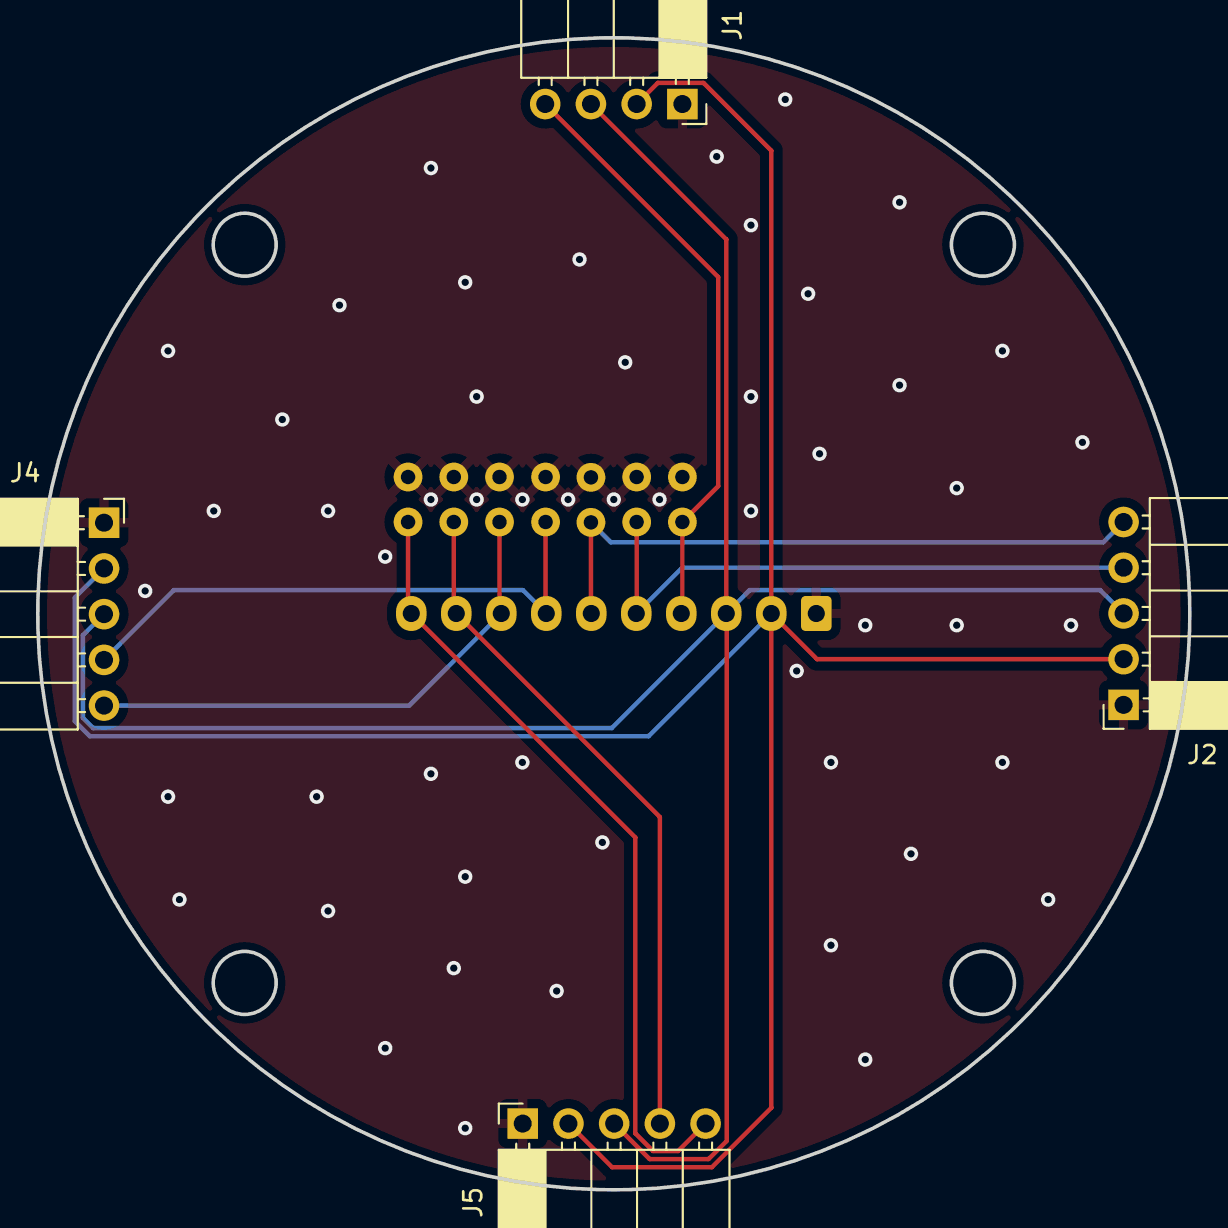
[picture p161: board line 統合.kicad_pcb from above]

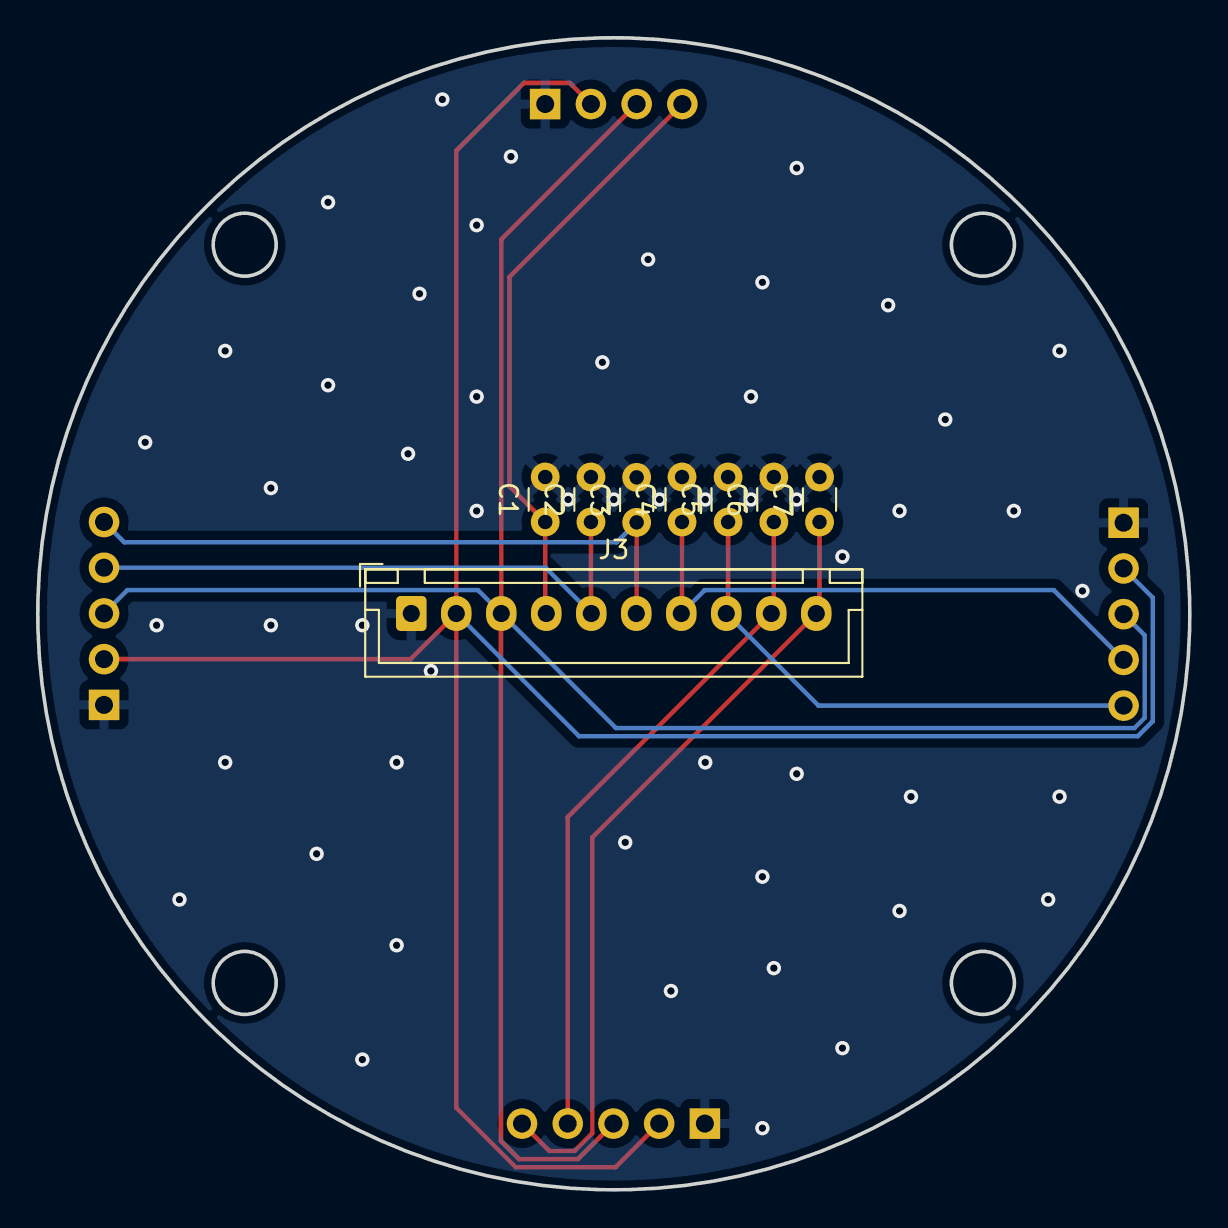
[picture p162: board line 統合.kicad_pcb from below]

Board: 2 copper layers, 64.0 x 64.0 mm, 12 parts (8 on the bottom side), 10 nets.

Parts:
C1, C2, C3, C4, C5, C6, C7: C_Small; C_Disc_D3.0mm_W1.6mm_P2.50mm
J1: Conn_01x04_Female; PinSocket_1x04_P2.54mm_Horizontal
J2, J4, J5: Conn_01x05_Female; PinSocket_1x05_P2.54mm_Horizontal
J3: Conn_01x10_Female; JST_XH_B10B-XH-A_1x10_P2.50mm_Vertical

Connections:
Line Left 1: C4.1, J3.7, J4.4
+5V: J1.2, J2.2, J3.2, J4.2, J5.2
GND: C1.2, C2.2, C3.2, C4.2, C5.2, C6.2, C7.2, J1.1, J2.1, J3.1, J4.1, J5.1
Line Back 1: C6.1, J3.9, J5.4
Line Back 2: C7.1, J3.10, J5.5
Line Front: C1.1, J1.4, J3.4
Line Left 2: C5.1, J3.8, J4.5
Line Right 1: C2.1, J2.4, J3.5
Line Right 2: C3.1, J2.5, J3.6
可変: J1.3, J2.3, J3.3, J4.3, J5.3
