MUNAKATA-EPC/Artemis_2023/KiCad_Projects/2022 late/Teensy_ver/kikker_PSU/kikker_PSU.kicad_pcb

## KiCad design KiCad_Projects/2022 late/Teensy_ver/kikker_PSU/kikker_PSU.kicad_pcb (2023-03-06)

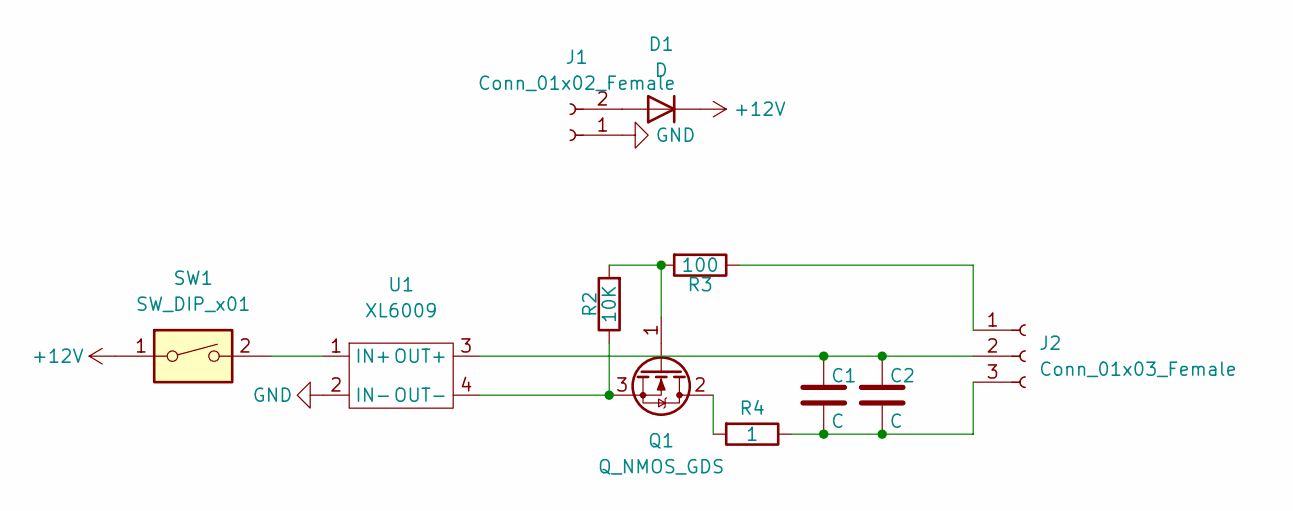
[picture p163: schematic kikker_PSU.kicad_sch]

Parts:
C1, C2: C; C_Radial_D16.0mm_H31.5mm_P7.50mm
D1: D; D_DO-15_P10.16mm_Horizontal
J1: Conn_01x02_Female; JST_XH_B2B-XH-A_1x02_P2.50mm_Vertical
J2: Conn_01x03_Female; JST_XH_B3B-XH-A_1x03_P2.50mm_Vertical
Q1: Q_NMOS_GDS; K15A20D
R2: 10K; R_Axial_DIN0204_L3.6mm_D1.6mm_P5.08mm_Horizontal
R3: 100; R_Axial_DIN0204_L3.6mm_D1.6mm_P5.08mm_Horizontal
R4: 1; 5W 1Ω sement
SW1: SW_DIP_x01; 2MS1T2B4M2QES
U1: XL6009

Connections:
+12V: D1.1 (K), SW1.1
GND: J1.1, U1.2 (IN-)
unnamed: C1.1, C2.1, J2.2, U1.3 (OUT+)
unnamed: C1.2, C2.2, J2.3, R4.1
unnamed: D1.2 (A), J1.2
unnamed: J2.1, R3.1
unnamed: Q1.1 (G), R2.2, R3.2
unnamed: Q1.2 (D), R4.2
unnamed: Q1.3 (S), R2.1, U1.4 (OUT-)
unnamed: SW1.2, U1.1 (IN+)

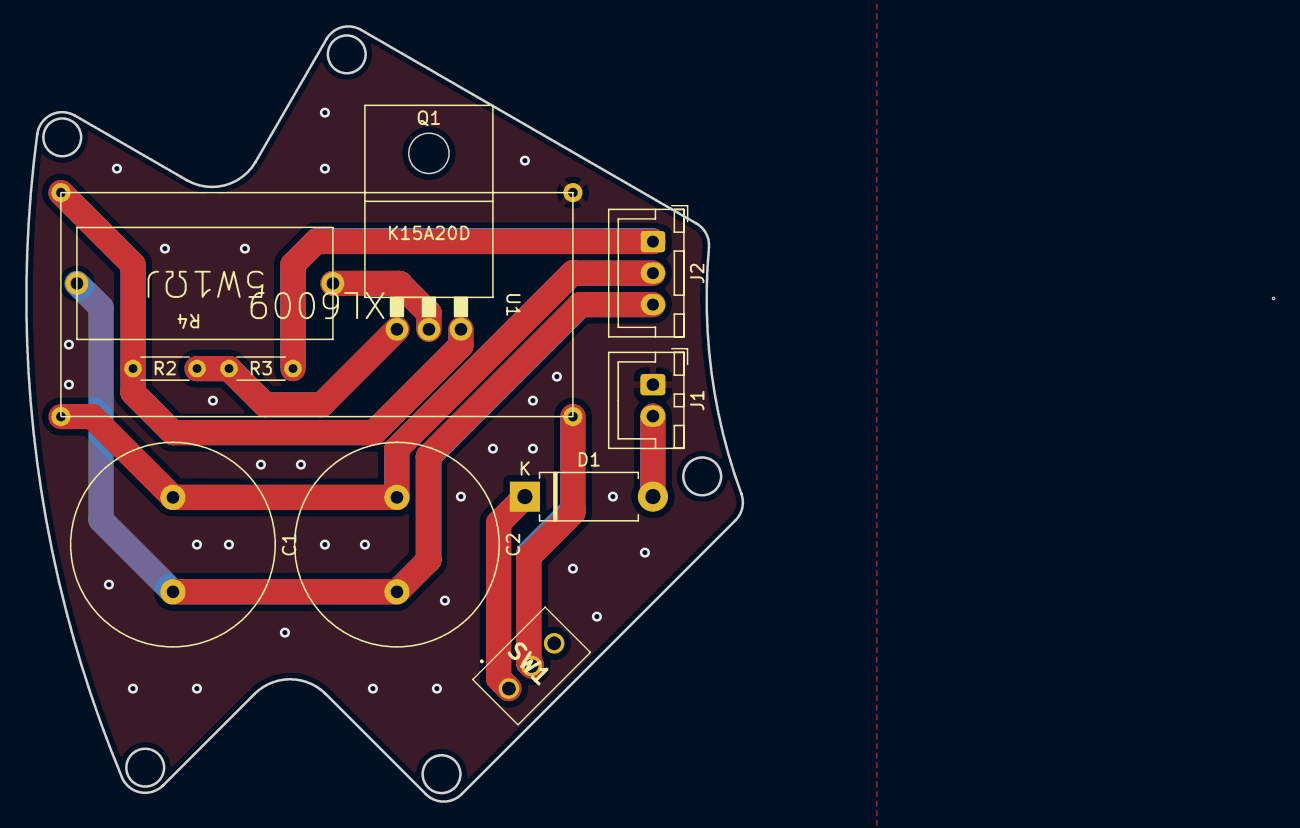
[picture p164: board kikker_PSU.kicad_pcb from above]

Board: 2 copper layers, 56.9 x 61.5 mm, 11 parts (0 on the bottom side), 10 nets.
