MUNAKATA-EPC/Artemis_2023/KiCad_Projects/2022 late/Teensy_ver/IO_Board_Teensy/IO_Board.kicad_pcb

## KiCad design KiCad_Projects/2022 late/Teensy_ver/IO_Board_Teensy/IO_Board.kicad_pcb (2023-03-06, an earlier design)

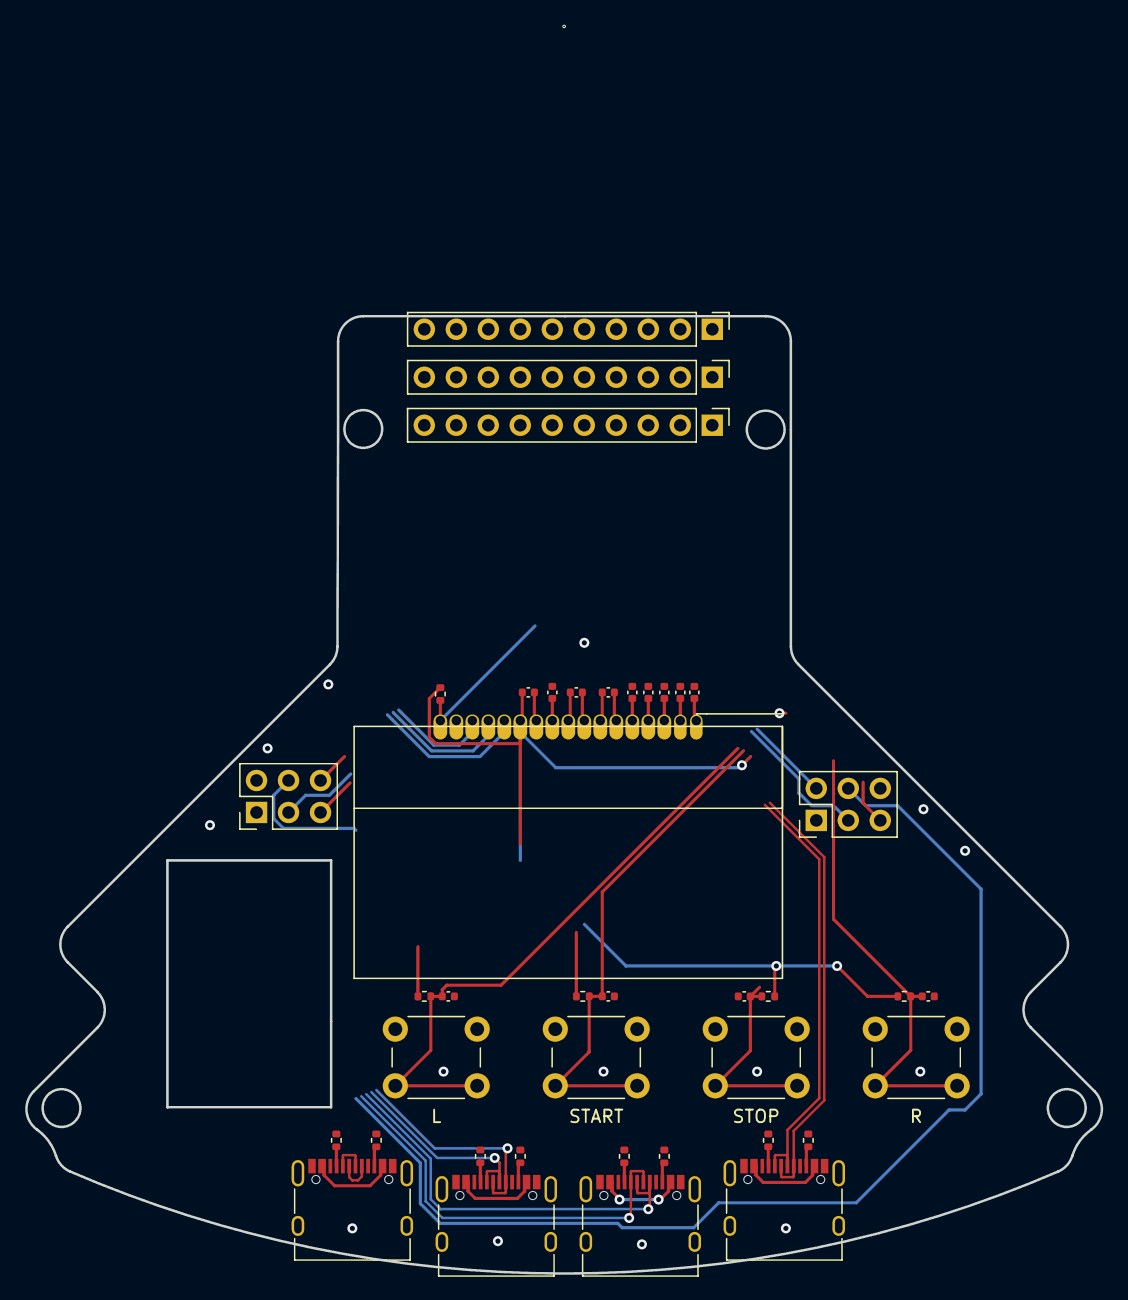
[picture p165: board KiCad_Projects/2022 late/Teensy_ver/IO_Board_Teensy/IO_Board.kicad_pcb from above]

Board: 2 copper layers, 85.4 x 76.0 mm, 40 parts (0 on the bottom side), 45 nets.

Parts:
C1, C2, C9, C13: C; C_0402_1005Metric
C3, C4, C5, C6, C7, C8, C10, C11, C12: C_Small; C_0402_1005Metric
J1, J4, J7, J10: USB_C_Receptacle_USB2.0; USB_C_Receptacle_XKB_U262-16XN-4BVC11
J2, J9: Conn_01x06_Female; PinHeader_2x03_P2.54mm_Vertical
J3, J5, J8: Conn_01x10_Female; PinHeader_1x10_P2.54mm_Vertical
J6: Conn_01x17_Female; LCDmodule_aqm1248a
L: SW_DIP_x01; SW_PUSH_6mm_H5mm
R: SW_DIP_x01; SW_PUSH_6mm_H5mm
R1, R4, R5, R8, R9: 10K; R_0402_1005Metric
R2, R3, R6, R7, R10, R11, R12, R13: R; R_0402_1005Metric
START: SW_DIP_x01; SW_PUSH_6mm_H5mm
STOP: SW_DIP_x01; SW_PUSH_6mm_H5mm

Connections:
+3V3: C4.2, J5.2, J6.6, R1.1, R4.2, R5.1, R8.1, R9.1
+5V: J2.4, J8.2, J9.4
CS: J5.7, J6.1, R4.1
Cam D+: J3.9, J4.A6 (D+), J4.B6 (D+)
Cam D-: J3.10, J4.A7 (D-), J4.B7 (D-)
GND: C1.2, C2.2, C3.1, C4.1, C7.1, C8.1, C9.2, C10.1, C11.1, C12.1, C13.2, J1.A1 (GND), J1.A12 (GND), J1.B1 (GND), J1.B12 (GND), J1.S1 (SHIELD), J2.1, J3.1, J3.2, J4.A1 (GND), J4.A12 (GND), J4.B1 (GND), J4.B12 (GND), J4.S1 (SHIELD), J5.1, J6.7, J7.A1 (GND), J7.A12 (GND), J7.B1 (GND), J7.B12 (GND), J7.S1 (SHIELD), J8.1, J9.1, J10.A1 (GND), J10.A12 (GND), J10.B1 (GND), J10.B12 (GND), J10.S1 (SHIELD), L.1, R.1, R2.2, R3.2, R6.2, R7.2, R10.2, R11.2, R12.2, R13.2, START.1, STOP.1
Gyro D+: J3.3, J7.A6 (D+), J7.B6 (D+)
Gyro D-: J3.4, J7.A7 (D-), J7.B7 (D-)
L: C13.1, J5.6, L.2, R9.2
Line D+: J3.5, J10.A6 (D+), J10.B6 (D+)
Line D-: J3.6, J10.A7 (D-), J10.B7 (D-)
MISO 1: J2.3, J8.4
MISO 2: J8.8, J9.3
MOSI: J5.8, J6.5
MOSI 1: J2.6, J8.5
MOSI 2: J8.9, J9.6
unnamed: C3.2, J6.8
unnamed: C5.1, J6.9
unnamed: C5.2, J6.10
unnamed: C6.1, J6.11
unnamed: C6.2, J6.12
unnamed: C7.2, J6.13
unnamed: C8.2, J6.14
unnamed: C10.2, J6.15
unnamed: C11.2, J6.16
unnamed: C12.2, J6.17
unnamed: J1.A5 (CC1), R2.1
unnamed: J1.B5 (CC2), R3.1
unnamed: J4.A5 (CC1), R6.1
unnamed: J4.B5 (CC2), R7.1
unnamed: J7.A5 (CC1), R10.1
unnamed: J7.B5 (CC2), R11.1
unnamed: J10.A5 (CC1), R12.1
unnamed: J10.B5 (CC2), R13.1
R: C9.1, J5.5, R.2, R8.2
RS: J5.9, J6.3
Reset 1: J2.2, J8.3
Reset 2: J8.7, J9.2
SCK: J5.10, J6.4
SCK 1: J2.5, J8.6
SCK 2: J8.10, J9.5
Teensy D+: J1.A6 (D+), J1.B6 (D+), J3.7
Teensy D-: J1.A7 (D-), J1.B7 (D-), J3.8
start: C1.1, J5.3, R1.2, START.2
stop: C2.1, J5.4, R5.2, STOP.2
