MUNAKATA-EPC/Artemis_2023/KiCad_Projects/その他/tj3b/tj3b core/tj3b core/TJ3B.kicad_pcb

## KiCad design KiCad_Projects/その他/tj3b/tj3b core/tj3b core/TJ3B.kicad_pcb (2022-06-01)

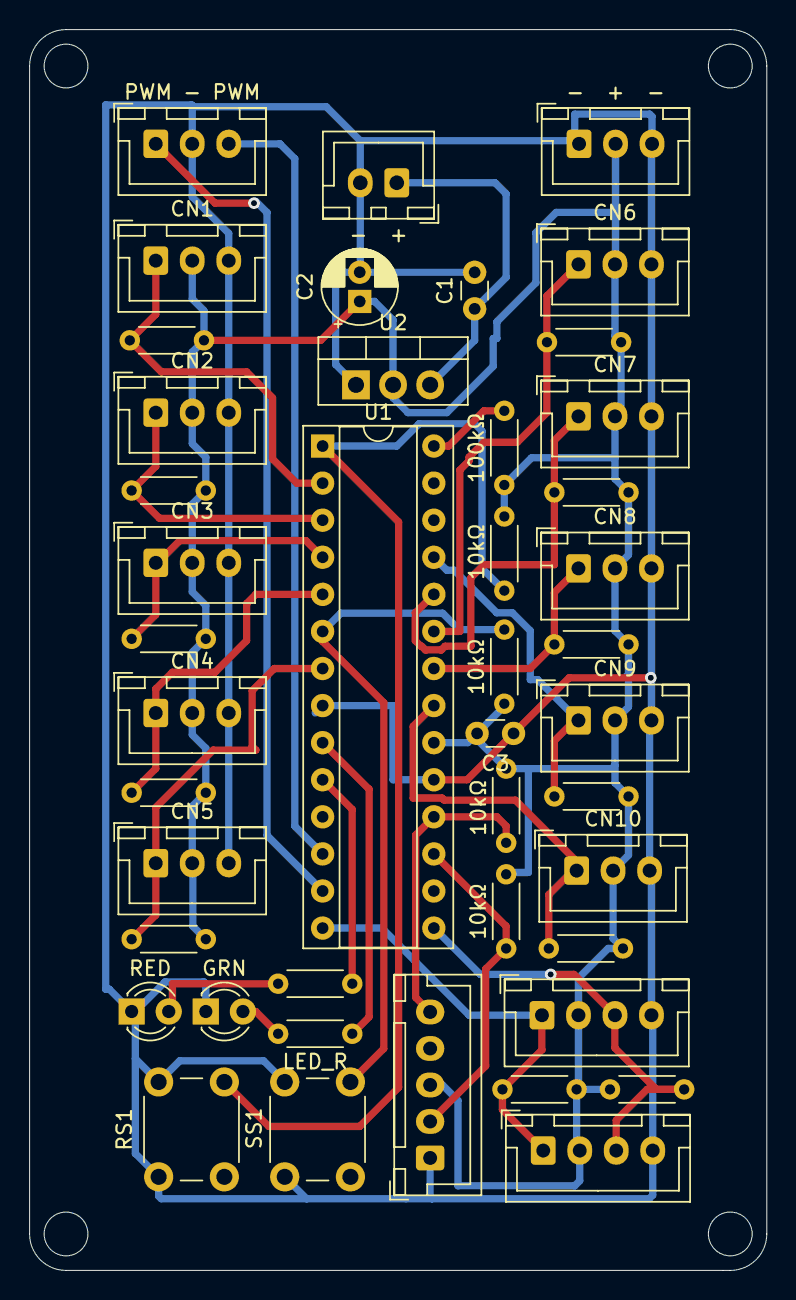
[picture p166: board KiCad_Projects/その他/tj3b/tj3b core/tj3b core/TJ3B.kicad_pcb from above]

Board: 2 copper layers, 50.5 x 85.0 mm, 28 parts (0 on the bottom side), 22 nets.

Parts:
10kΩ, 10kΩ#2, 10kΩ#3, 10kΩ#4: R; R_Axial_DIN0204_L3.6mm_D1.6mm_P5.08mm_Horizontal
100kΩ: 100kΩ; R_Axial_DIN0204_L3.6mm_D1.6mm_P5.08mm_Horizontal
-  +: Conn_01x02_Female; JST_XH_B2B-XH-A_1x02_P2.50mm_Vertical
-  +  -: Conn_01x03_Female; JST_XH_B3B-XH-A_1x03_P2.50mm_Vertical
C1, C3: C; C_Disc_D3.0mm_W1.6mm_P2.50mm
C2: C; CP_Radial_D5.0mm_P2.00mm
CN1, CN2, CN3, CN4, CN5, CN6, CN7, CN8, CN9, CN10: Conn_01x03_Female; JST_XH_B3B-XH-A_1x03_P2.50mm_Vertical
GRN: LED; LED_D3.0mm
LED_R: R; R_Axial_DIN0204_L3.6mm_D1.6mm_P5.08mm_Horizontal
PWM - PWM: Conn_01x03_Female; JST_XH_B3B-XH-A_1x03_P2.50mm_Vertical
RED: LED; LED_D3.0mm
RS1: SW_Push; SW_PUSH_6mm
SS1: SW_Push; SW_PUSH_6mm
U1: TJ3_mein; DIP-28_W7.62mm_Socket
U2: AMS1117-1.5; TO-220-3_Vertical

Connections:
+5V: 10kΩ.1, 10kΩ#2.2, 10kΩ#3.1, 10kΩ#4.2, 100kΩ.1, - + -.2, C2.1, C3.2, CN1.2, CN2.2, CN3.2, CN4.2, CN5.2, CN6.2, CN7.2, CN8.2, CN9.2, CN10.2, U1.20, U2.2
AD1: CN1.1, U1.2
AD2: CN2.1, U1.3
AD3: CN3.1, U1.4
AD4: CN4.1, U1.5
AD5: CN5.1, U1.7
AD6: CN6.1, U1.23
AD7: CN7.1, U1.24
AD8: CN8.1, U1.22
AD9: CN9.1, U1.25
AD10: CN10.1, U1.21
GND: - +.2, - + -.1, - + -.3, C1.2, C2.2, C3.1, CN1.3, CN2.3, CN3.3, CN4.3, CN5.3, CN6.3, CN7.3, CN8.3, CN9.3, CN10.3, GRN.1, PWM - PWM.2, RED.1, RS1.2, SS1.2, U1.8, U1.19, U2.1
MCLR: 10kΩ#2.1, RS1.1, U1.1
unnamed: - +.1, C1.1, U2.3
unnamed: GRN.2, LED_R.1
PGD_×: 100kΩ.2, U1.28
PWM1: PWM - PWM.3, U1.12
PWM2: PWM - PWM.1, U1.13
PWR_LED: LED_R.2, U1.9
RA4: 10kΩ.2, SS1.1, U1.6
RX: 10kΩ#3.2, U1.18
TX: 10kΩ#4.1, U1.17
