MUNAKATA-EPC/Artemis_2023/KiCad_Projects/その他/LSM6DS3_Gyro/LSM6DS3_Gyro.kicad_pcb

## KiCad design KiCad_Projects/その他/LSM6DS3_Gyro/LSM6DS3_Gyro.kicad_pcb (2022-10-13)

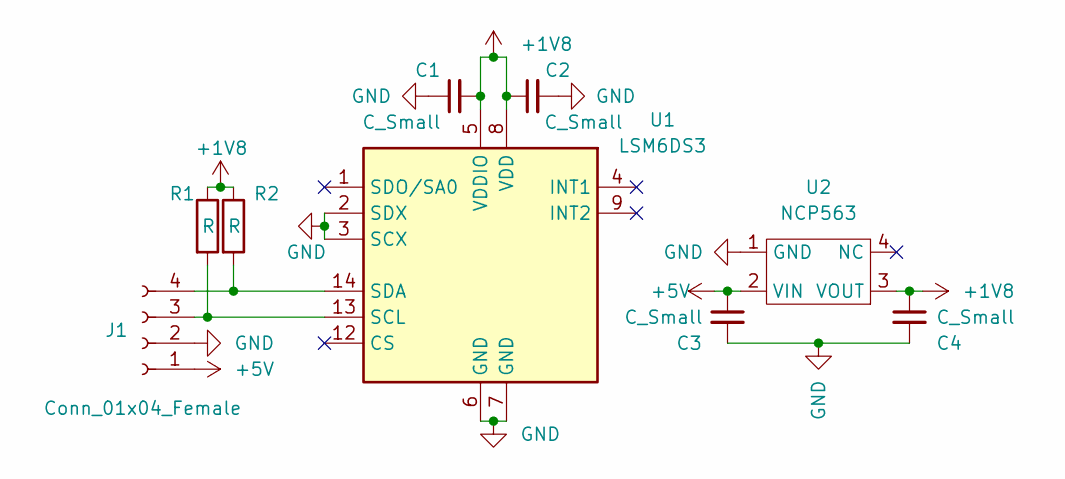
[picture p167: schematic LSM6DS3_Gyro.kicad_sch]

Parts:
C1, C2, C3, C4: C_Small; C_0201_0603Metric
J1: Conn_01x04_Female; PinHeader_1x04_P2.54mm_Vertical
R1, R2: R; R_0201_0603Metric
U1: LSM6DS3; LGA-14_3x2.5mm_P0.5mm_LayoutBorder3x4y
U2: NCP563

Connections:
+1V8: C1.2, C2.1, C4.1, R1.1, R2.1, U1.5 (VDDIO), U1.8 (VDD), U2.3 (VOUT)
+5V: C3.1, J1.1, U2.2 (VIN)
GND: C1.1, C2.2, C3.2, C4.2, J1.2, U1.2 (SDX), U1.3 (SCX), U1.6 (GND), U1.7 (GND), U2.1 (GND)
unnamed: J1.3, R1.2, U1.13 (SCL)
unnamed: J1.4, R2.2, U1.14 (SDA)

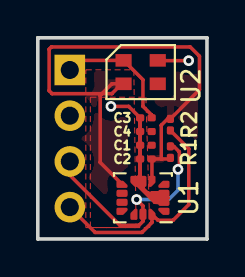
[picture p168: board LSM6DS3_Gyro.kicad_pcb from above]

Board: 2 copper layers, 9.4 x 11.2 mm, 9 parts (1 on the bottom side), 5 nets.
