MUNAKATA-EPC/Artemis_2023/KiCad_Projects/その他/MPU6050/AT.kicad_pcb

## KiCad design KiCad_Projects/その他/MPU6050/AT.kicad_pcb (2023-03-06)

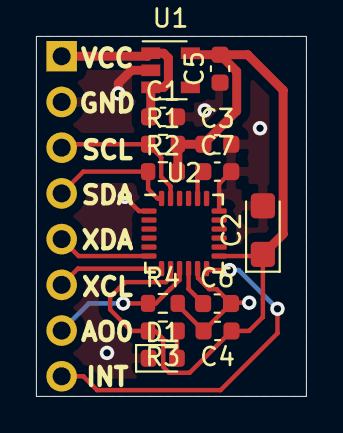
[picture p169: board KiCad_Projects/その他/MPU6050/AT.kicad_pcb from above]

Board: 2 copper layers, 15.0 x 20.0 mm, 15 parts (1 on the bottom side), 12 nets.

Parts:
C1, C3, C4, C5, C6, C7: C_Small; C_0603_1608Metric
C2: C_Small; CP_EIA-3216-10_Kemet-I
D1: LED; LED_0603_1608Metric
J1: Conn_01x08; PinHeader_1x08_P2.54mm_Vertical
R1, R2, R3, R4: R_Small; R_0603_1608Metric
U1: TLV713185PDBV; SOT-23-5
U2: MPU-6050; InvenSense_QFN-24_4x4mm_P0.5mm

Connections:
+3V3: C2.1, C3.1, C4.1, C5.2, R1.2, R2.2, R3.2, U1.5, U2.8, U2.13
+5V: C1.1, J1.1, U1.1, U1.3
/AD0: J1.7, R4.1, U2.9
/INT: J1.8, U2.12
/SCL: J1.3, R1.1, U2.23
/SDA: J1.4, R2.1, U2.24
/XCL: J1.6, U2.7
/XDA: J1.5, U2.6
GND: C1.2, C2.2, C3.2, C4.2, C5.1, C6.2, C7.2, D1.1, J1.2, R4.2, U1.2, U2.1, U2.11, U2.18
unnamed: C6.1, U2.10
unnamed: C7.1, U2.20
unnamed: D1.2, R3.1
