MUNAKATA-EPC/Artemis_2023/KiCad_Projects/2022 late/main_board_Freerouting/main_board_Teensy.kicad_pcb

## KiCad design KiCad_Projects/2022 late/main_board_Freerouting/main_board_Teensy.kicad_pcb (2023-03-06)

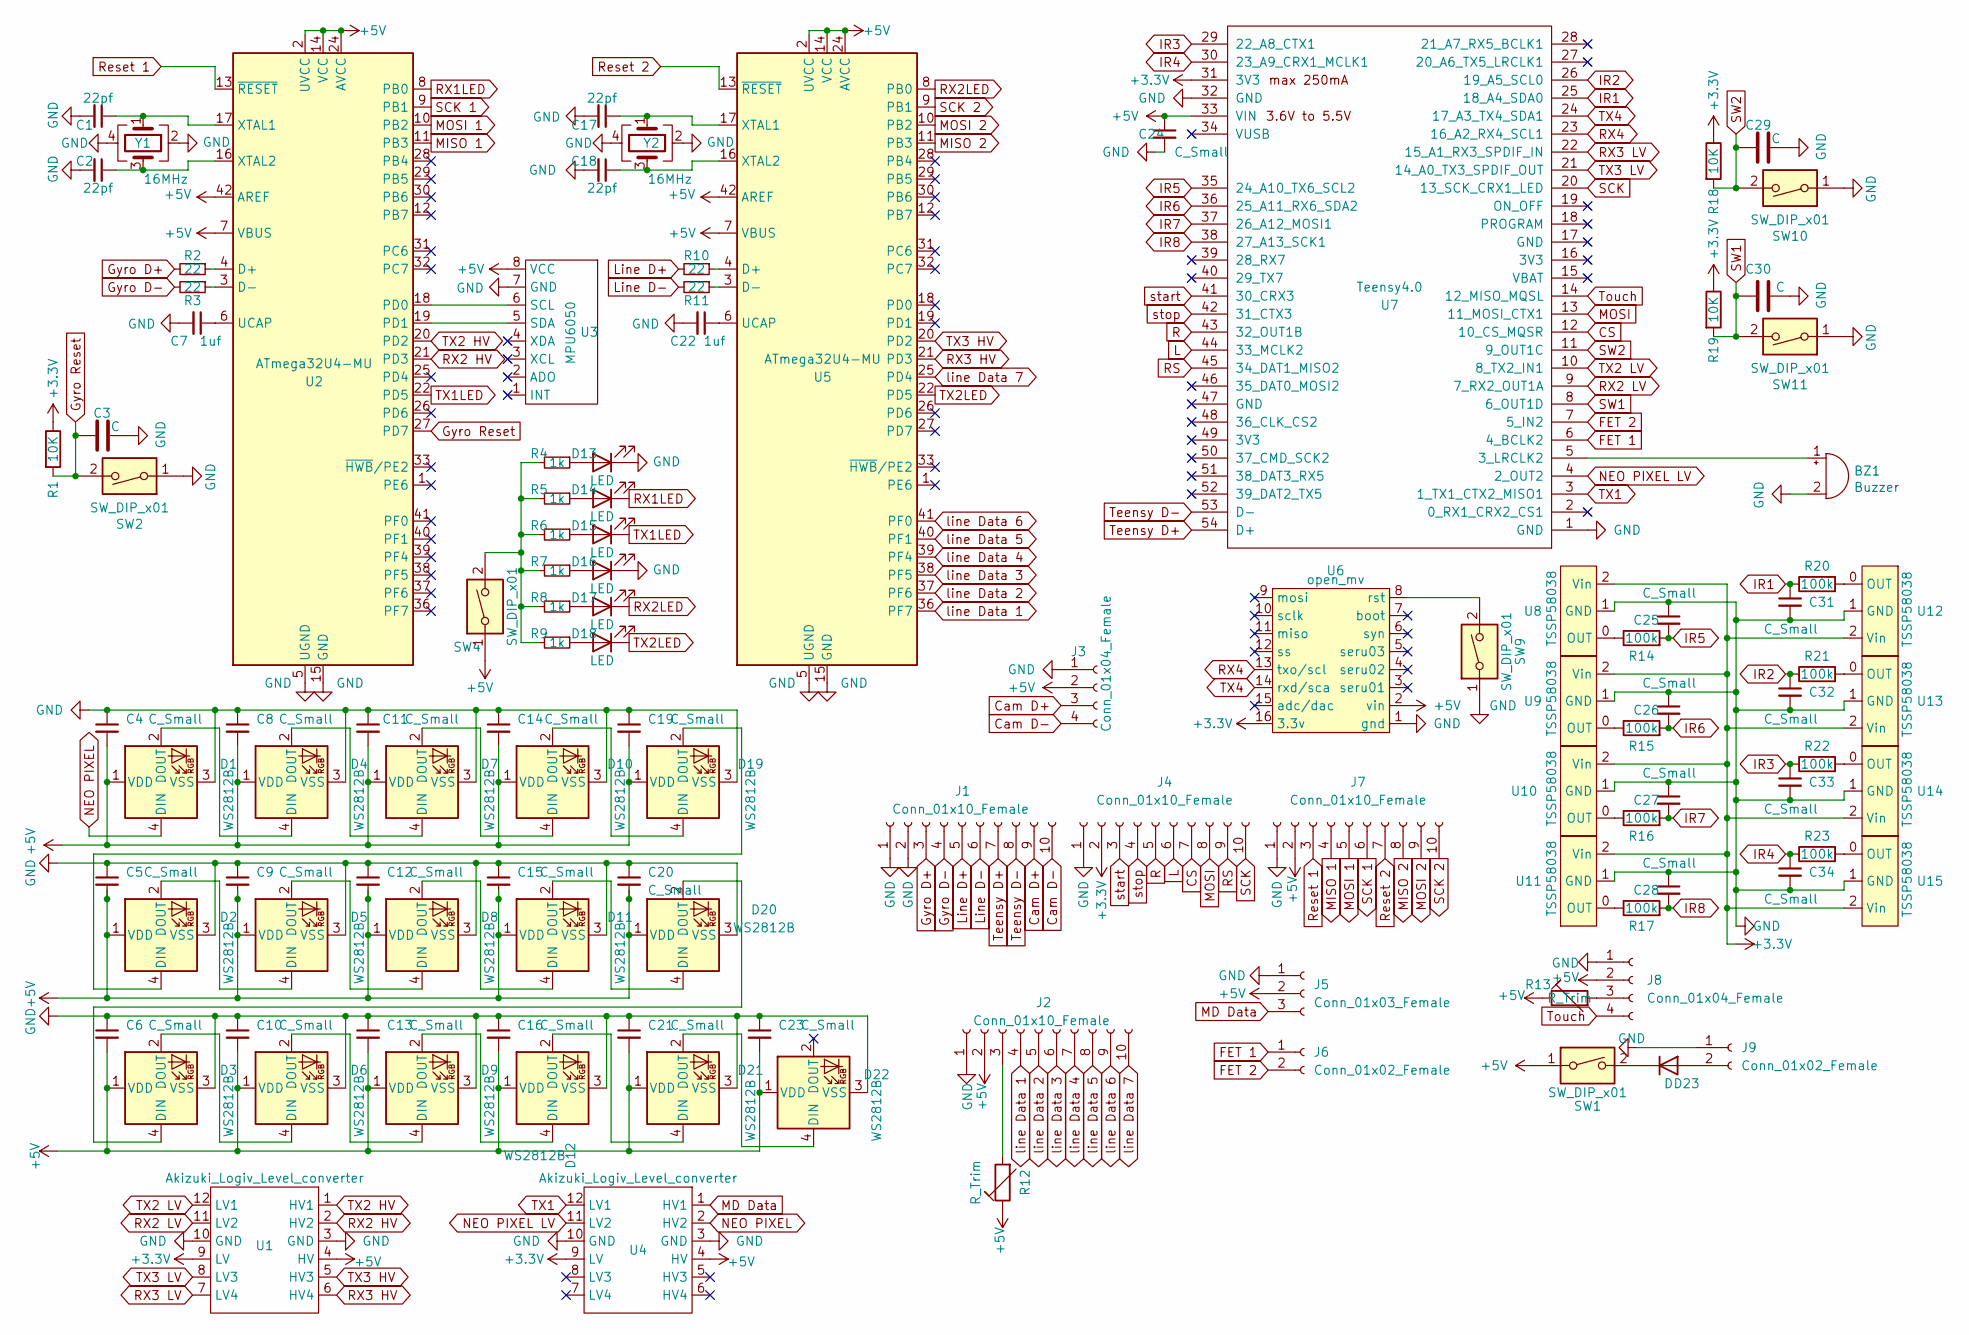
[picture p170: schematic main_board_Teensy.kicad_sch, 2022 Late Main Board Teensy]

Parts:
BZ1: Buzzer; Buzzer_12x9.5RM7.6
C1, C2, C17, C18: 22pf; C_0402_1005Metric; LCSC C1555
C3, C29, C30: C; C_0402_1005Metric; LCSC C507422
C4, C5, C6, C8, C9, C10, C11, C12, C13, C14, C15, C16, C19, C20, C21, C23, C24, C25, C26, C27, C28, C31, C32, C33, C34: C_Small; C_0402_1005Metric; LCSC C507422
C7, C22: 1uf; C_0402_1005Metric; LCSC C52923
D1, D2, D3, D5, D6, D7, D8, D9, D10, D11, D12, D19, D20, D21, D22: WS2812B; LED_WS2812B_PLCC4_5.0x5.0mm_P3.2mm; LCSC C2761795
D4: WS2812B; LED_WS2812B_PLCC4_5.0x5.0mm_P3.2mm
D13, D14, D15, D16, D17, D18: LED; LED_0402_1005Metric; LCSC C130725
D23: D; D_A-405_P7.62mm_Horizontal
J1, J4, J7: Conn_01x10_Female; PinHeader_1x10_P2.54mm_Vertical
J2: Conn_01x10_Female; JST_XH_S10B-XH-A-1_1x10_P2.50mm_Horizontal
J3: Conn_01x04_Female; PinHeader_1x04_P2.54mm_Vertical
J5: Conn_01x03_Female; JST_XH_B3B-XH-A_1x03_P2.50mm_Vertical
J6, J9: Conn_01x02_Female; JST_XH_B2B-XH-A_1x02_P2.50mm_Vertical
J8: Conn_01x04_Female; JST_XH_B4B-XH-A_1x04_P2.50mm_Vertical
R1, R18, R19: 10K; R_0402_1005Metric; LCSC C269674
R2, R3, R10, R11: 22; R_0402_1005Metric; LCSC C25092
R4, R5, R6, R7, R8, R9: 1k; R_0402_1005Metric; LCSC C11702
R12, R13: R_Trim; 可変抵抗(小)
R14, R15, R16, R17, R20, R21, R22, R23: 100k; R_0402_1005Metric; LCSC C269673
SW1, SW4: SW_DIP_x01; 2MS1T2B4M2QES
SW2, SW9, SW10, SW11: SW_DIP_x01; SW_PUSH_6mm_H5mm
U1, U4: Akizuki_Logiv_Level_converter; Akizuki_Logic_Level_converter
U2, U5: ATmega32U4-MU; QFN-44-1EP_7x7mm_P0.5mm_EP5.2x5.2mm; LCSC C112161
U3: MPU6050
U6: open_mv; OpenMV
U7: Teensy4.0; Teensy_Brakeout
U8, U9, U10, U11, U12, U13, U14, U15: TSSP58038; TSSP58038_IR
Y1, Y2: 16MHz; Crystal_SMD_3225-4Pin_3.2x2.5mm; LCSC C164049

Connections:
+3V3: J4.2, R1.1, R18.1, R19.1, U1.9 (LV), U4.9 (LV), U6.16 (3.3v), U7.31 (3V3), U8.2 (Vin), U9.2 (Vin), U10.2 (Vin), U11.2 (Vin), U12.2 (Vin), U13.2 (Vin), U14.2 (Vin), U15.2 (Vin)
+5V: C4.2, C5.2, C6.2, C8.2, C9.2, C10.2, C11.2, C12.2, C13.2, C14.2, C15.2, C16.2, C19.2, C20.2, C21.2, C23.2, C24.1, D1.1 (VDD), D2.1 (VDD), D3.1 (VDD), D4.1 (VDD), D5.1 (VDD), D6.1 (VDD), D7.1 (VDD), D8.1 (VDD), D9.1 (VDD), D10.1 (VDD), D11.1 (VDD), D12.1 (VDD), D19.1 (VDD), D20.1 (VDD), D21.1 (VDD), D22.1 (VDD), J2.2, J3.2, J5.2, J7.2, J8.2, R12.1, R13.1, SW1.1, SW4.1, U1.4 (HV), U2.2 (UVCC), U2.7 (VBUS), U2.14 (VCC), U2.24 (AVCC), U2.34 (VCC), U2.42 (AREF), U2.44 (AVCC), U3.8 (VCC), U4.4 (HV), U5.2 (UVCC), U5.7 (VBUS), U5.14 (VCC), U5.24 (AVCC), U5.34 (VCC), U5.42 (AREF), U5.44 (AVCC), U6.2 (vin), U7.33 (VIN)
CS: J4.7, U7.12 (10_CS_MQSR)
Cam D+: J1.9, J3.3
Cam D-: J1.10, J3.4
FET 1: J6.1, U7.6 (4_BCLK2)
FET 2: J6.2, U7.7 (5_IN2)
GND: BZ1.2 (+), C1.2, C2.2, C3.2, C4.1, C5.1, C6.1, C7.2, C8.1, C9.1, C10.1, C11.1, C12.1, C13.1, C14.1, C15.1, C16.1, C17.2, C18.2, C19.1, C20.1, C21.1, C22.2, C23.1, C24.2, C25.1, C26.1, C27.1, C28.1, C29.2, C30.2, C31.2, C32.2, C33.2, C34.2, D1.3 (VSS), D2.3 (VSS), D3.3 (VSS), D4.3 (VSS), D5.3 (VSS), D6.3 (VSS), D7.3 (VSS), D8.3 (VSS), D9.3 (VSS), D10.3 (VSS), D11.3 (VSS), D12.3 (VSS), D13.1 (K), D16.1 (K), D19.3 (VSS), D20.3 (VSS), D21.3 (VSS), D22.3 (VSS), J1.1, J1.2, J2.1, J3.1, J4.1, J5.1, J7.1, J8.1, J9.1, SW2.1, SW9.1, SW10.1, SW11.1, U1.3 (GND), U1.10 (GND), U2.5 (UGND), U2.15 (GND), U2.23 (GND), U2.35 (GND), U2.43 (GND), U2.45 (GND), U3.7 (GND), U4.3 (GND), U4.10 (GND), U5.5 (UGND), U5.15 (GND), U5.23 (GND), U5.35 (GND), U5.43 (GND), U5.45 (GND), U6.1 (gnd), U7.1 (GND), U7.32 (GND), U8.1 (GND), U9.1 (GND), U10.1 (GND), U11.1 (GND), U12.1 (GND), U13.1 (GND), U14.1 (GND), U15.1 (GND), Y1.2, Y1.4, Y2.2, Y2.4; also elsewhere on the board
Gyro D+: J1.3, R2.2
Gyro D-: J1.4, R3.2
Gyro Reset: C3.1, R1.2, SW2.2, U2.27 (PD7); also elsewhere on the board
IR1: C31.1, R20.1, U7.25 (18_A4_SDA0)
IR2: C32.1, R21.1, U7.26 (19_A5_SCL0)
IR3: C33.1, R22.1, U7.29 (22_A8_CTX1)
IR4: C34.1, R23.1, U7.30 (23_A9_CRX1_MCLK1)
IR5: C25.2, R14.2, U7.35 (24_A10_TX6_SCL2)
IR6: C26.2, R15.2, U7.36 (25_A11_RX6_SDA2)
IR7: C27.2, R16.2, U7.37 (26_A12_MOSI1)
IR8: C28.2, R17.2, U7.38 (27_A13_SCK1)
L: J4.6, U7.44 (33_MCLK2)
Line D+: J1.5, R10.2
Line D-: J1.6, R11.2
MD Data: J5.3, U4.1 (HV1)
MISO 1: J7.4, U2.11 (PB3)
MISO 2: J7.8, U5.11 (PB3)
MOSI: J4.8, U7.13 (11_MOSI_CTX1)
MOSI 1: J7.5, U2.10 (PB2)
MOSI 2: J7.9, U5.10 (PB2)
NEO PIXEL: D1.4 (DIN), U4.2 (HV2)
NEO PIXEL LV: U4.11 (LV2), U7.4 (2_OUT2)
unnamed: BZ1.1 (-), U7.5 (3_LRCLK2)
unnamed: C1.1, U2.17 (XTAL1), Y1.1
unnamed: C2.1, U2.16 (XTAL2), Y1.3
unnamed: C7.1, U2.6 (UCAP)
unnamed: C17.1, U5.17 (XTAL1), Y2.1
unnamed: C18.1, U5.16 (XTAL2), Y2.3
unnamed: C22.1, U5.6 (UCAP)
unnamed: D1.2 (DOUT), D4.4 (DIN)
unnamed: D2.2 (DOUT), D5.4 (DIN)
unnamed: D3.2 (DOUT), D6.4 (DIN)
unnamed: D4.2 (DOUT), D7.4 (DIN)
unnamed: D5.2 (DOUT), D8.4 (DIN)
unnamed: D6.2 (DOUT), D9.4 (DIN)
unnamed: D10.2 (DOUT), D19.4 (DIN)
unnamed: D7.2 (DOUT), D10.4 (DIN)
unnamed: D11.2 (DOUT), D20.4 (DIN)
unnamed: D8.2 (DOUT), D11.4 (DIN)
unnamed: D12.2 (DOUT), D21.4 (DIN)
unnamed: D9.2 (DOUT), D12.4 (DIN)
unnamed: D13.2 (A), R4.1
unnamed: D14.2 (A), R5.1
unnamed: D15.2 (A), R6.1
unnamed: D16.2 (A), R7.1
unnamed: D17.2 (A), R8.1
unnamed: D18.2 (A), R9.1
unnamed: D2.4 (DIN), D19.2 (DOUT)
unnamed: D3.4 (DIN), D20.2 (DOUT)
unnamed: D21.2 (DOUT), D22.4 (DIN)
unnamed: D23.1 (K), SW1.2
unnamed: D23.2 (A), J9.2
unnamed: J2.3, R12.2
unnamed: J8.3, R13.2
unnamed: R2.1, U2.4 (D+)
unnamed: R3.1, U2.3 (D-)
unnamed: R4.2, R5.2, R6.2, R7.2, R8.2, R9.2, SW4.2
unnamed: R10.1, U5.4 (D+)
unnamed: R11.1, U5.3 (D-)
unnamed: R14.1, U8.0 (OUT)
unnamed: R15.1, U9.0 (OUT)
unnamed: R16.1, U10.0 (OUT)
unnamed: R17.1, U11.0 (OUT)
unnamed: R20.2, U12.0 (OUT)
unnamed: R21.2, U13.0 (OUT)
unnamed: R22.2, U14.0 (OUT)
unnamed: R23.2, U15.0 (OUT)
unnamed: U2.18 (PD0), U3.6 (SCL)
unnamed: U2.19 (PD1), U3.5 (SDA)
unnamed 77: SW9.2, U6.8 (rst); also elsewhere on the board
R: J4.5, U7.43 (32_OUT1B)
RS: J4.9, U7.45 (34_DAT1_MISO2)
RX1LED: D14.1 (K), U2.8 (PB0)
RX2 HV: U1.2 (HV2), U2.21 (PD3)
RX2 LV: U1.11 (LV2), U7.9 (7_RX2_OUT1A)
RX2LED: D17.1 (K), U5.8 (PB0)
RX3 HV: U1.6 (HV4), U5.21 (PD3)
RX3 LV: U1.7 (LV4), U7.22 (15_A1_RX3_SPDIF_IN)
RX4: U6.13 (txo/scl), U7.23 (16_A2_RX4_SCL1)
Reset 1: J7.3, U2.13 (~RESET)
Reset 2: J7.7, U5.13 (~RESET)
SCK: J4.10, U7.20 (13_SCK_CRX1_LED)
SCK 1: J7.6, U2.9 (PB1)
SCK 2: J7.10, U5.9 (PB1)
SW1: C30.1, R19.2, SW11.2, U7.8 (6_OUT1D); also elsewhere on the board
SW2: C29.1, R18.2, SW10.2, U7.11 (9_OUT1C)
TX1: U4.12 (LV1), U7.3 (1_TX1_CTX2_MISO1)
TX1LED: D15.1 (K), U2.22 (PD5)
TX2 HV: U1.1 (HV1), U2.20 (PD2)
TX2 LV: U1.12 (LV1), U7.10 (8_TX2_IN1)
TX2LED: D18.1 (K), U5.22 (PD5)
TX3 HV: U1.5 (HV3), U5.20 (PD2)
TX3 LV: U1.8 (LV3), U7.21 (14_A0_TX3_SPDIF_OUT)
TX4: U6.14 (rxd/sca), U7.24 (17_A3_TX4_SDA1)
Teensy D+: J1.7, U7.54 (D+)
Teensy D-: J1.8, U7.53 (D-)
Touch: J8.4, U7.14 (12_MISO_MQSL)
line Data 1: J2.4, U5.36 (PF7)
line Data 2: J2.5, U5.37 (PF6)
line Data 3: J2.6, U5.38 (PF5)
line Data 4: J2.7, U5.39 (PF4)
line Data 5: J2.8, U5.40 (PF1)
line Data 6: J2.9, U5.41 (PF0)
line Data 7: J2.10, U5.25 (PD4)
start: J4.3, U7.41 (30_CRX3)
stop: J4.4, U7.42 (31_CTX3)

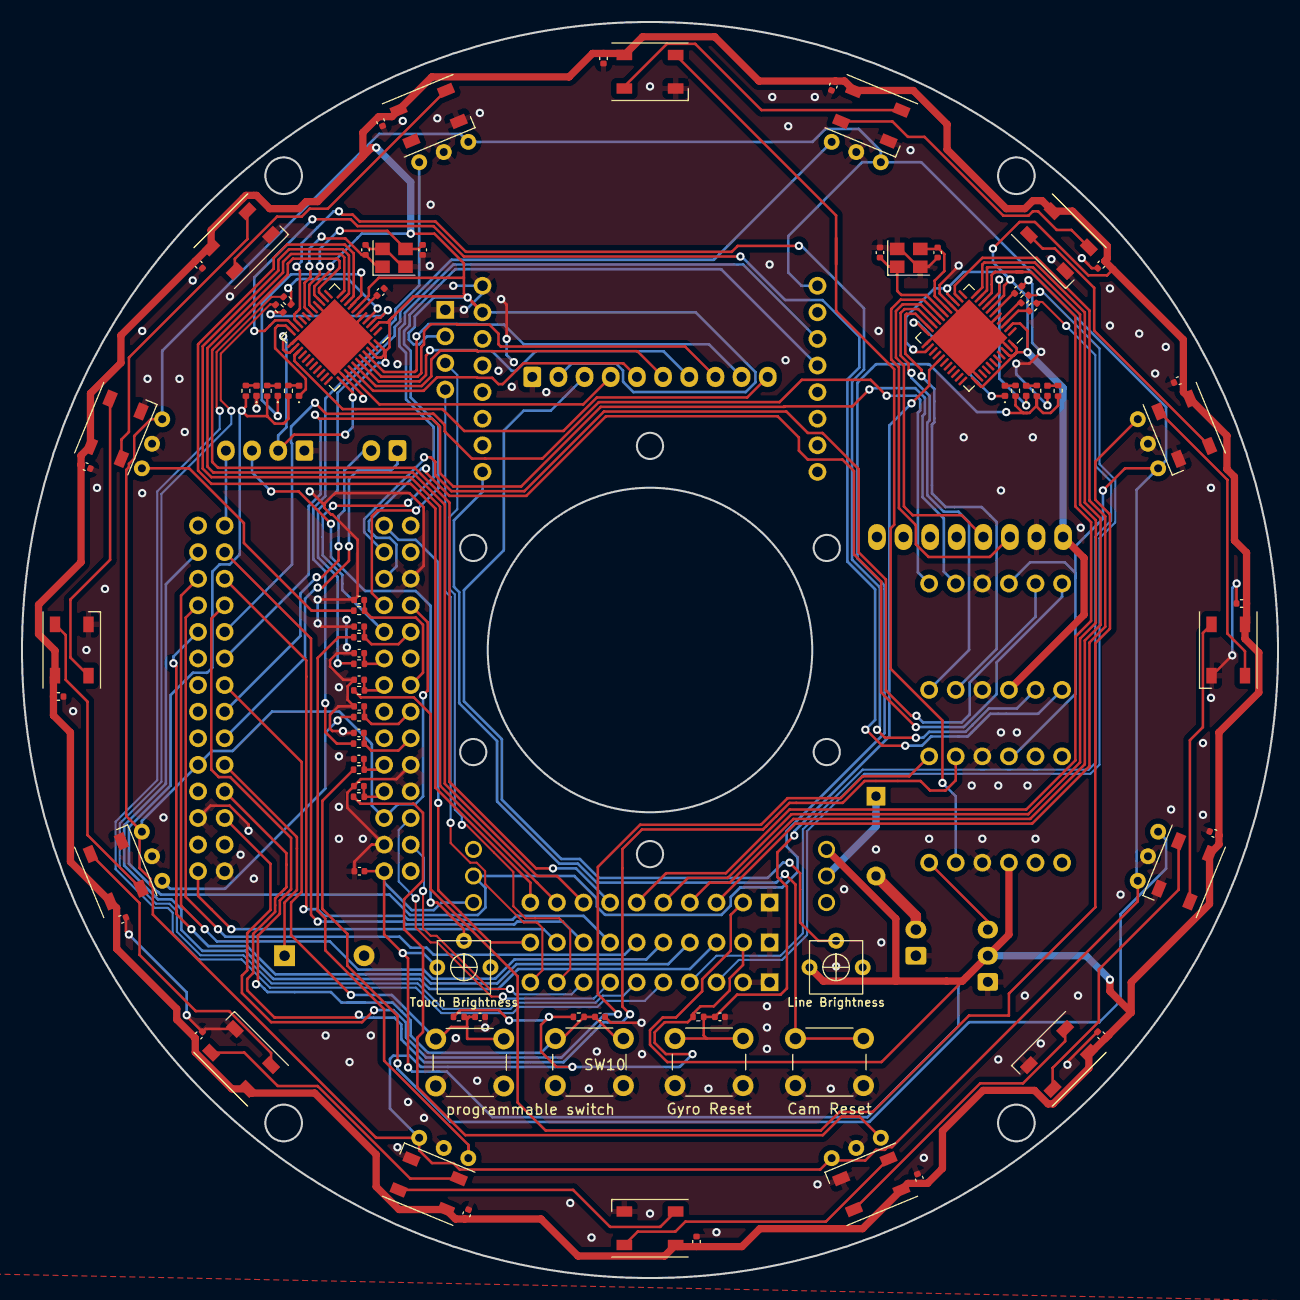
[picture p171: board main_board_Teensy.kicad_pcb from above]

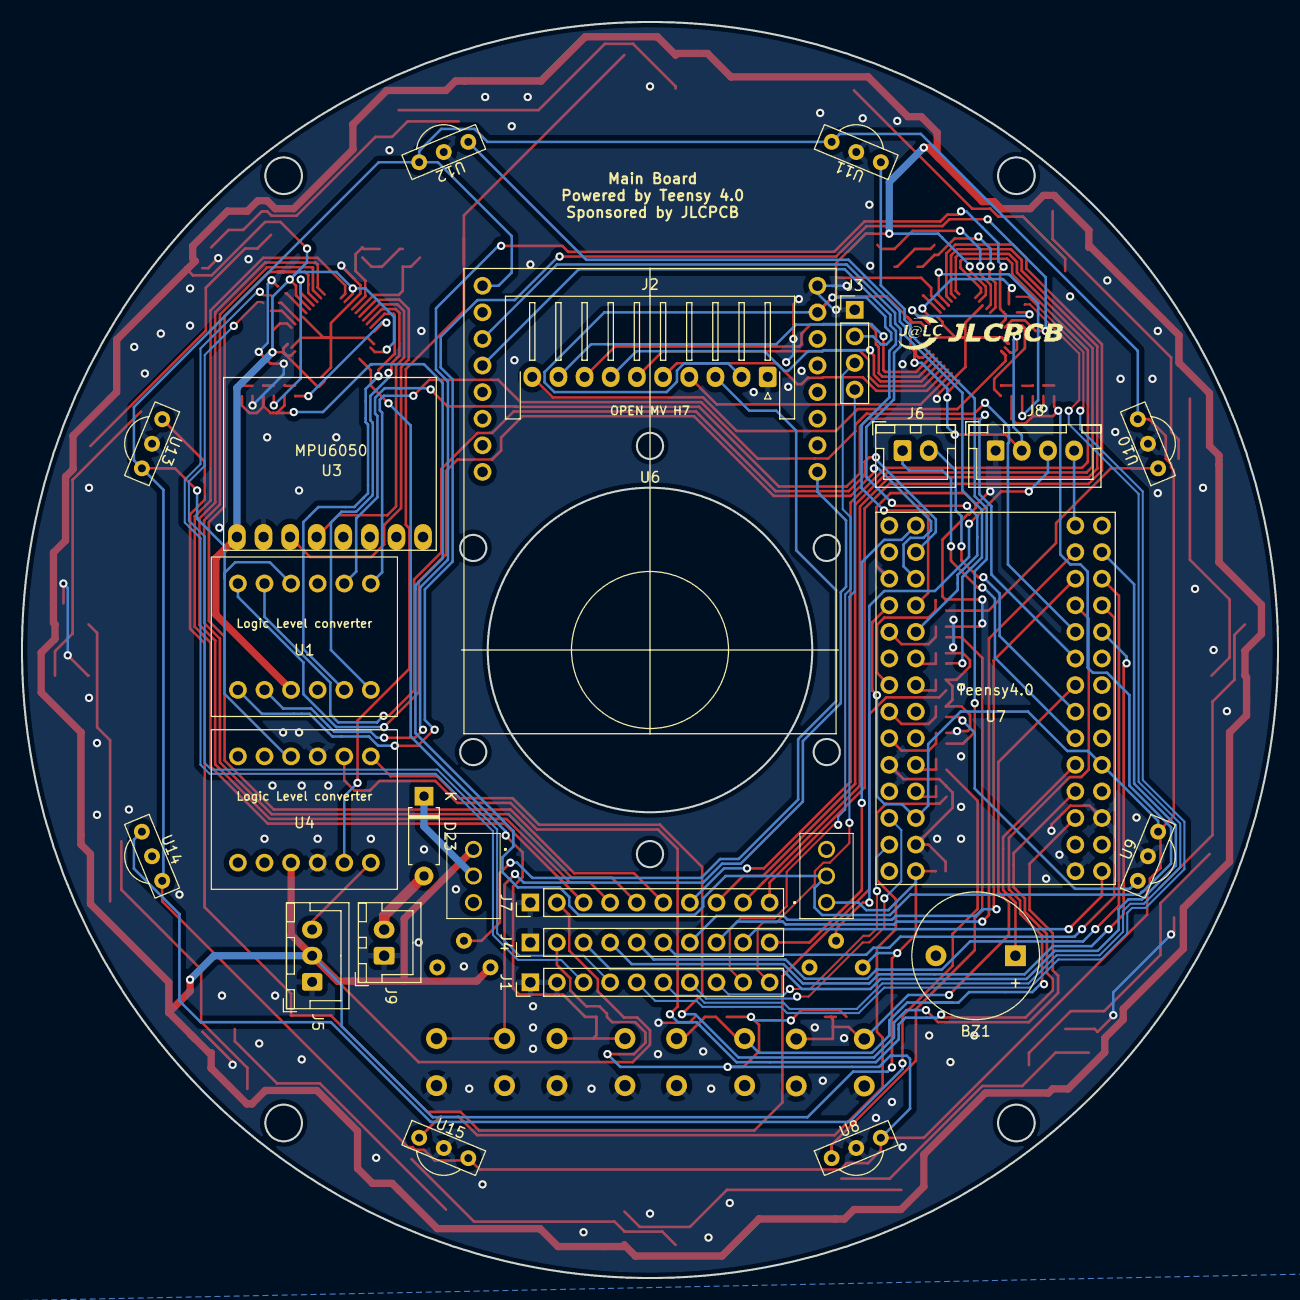
[picture p172: board main_board_Teensy.kicad_pcb from below]

Board: 2 copper layers, 120.0 x 120.0 mm, 113 parts (26 on the bottom side), 114 nets.

Other parts of the board:
Cam Reset: SW_DIP_x01; SW_PUSH_6mm_H5mm
Gyro Reset: SW_DIP_x01; SW_PUSH_6mm_H5mm
programmable switch: SW_DIP_x01; SW_PUSH_6mm_H5mm

Their connections:
GND: Cam Reset.1, Gyro Reset.1, programmable switch.1; also elsewhere on the board
Gyro Reset: Gyro Reset.2; also elsewhere on the board
unnamed 77: Cam Reset.2; also elsewhere on the board
SW1: programmable switch.2; also elsewhere on the board
