MUNAKATA-EPC/Artemis_2023/KiCad_Projects/その他/先輩の基板/ATXIAO/main.kicad_pcb

## KiCad design KiCad_Projects/その他/先輩の基板/ATXIAO/main.kicad_pcb (2022-10-13)

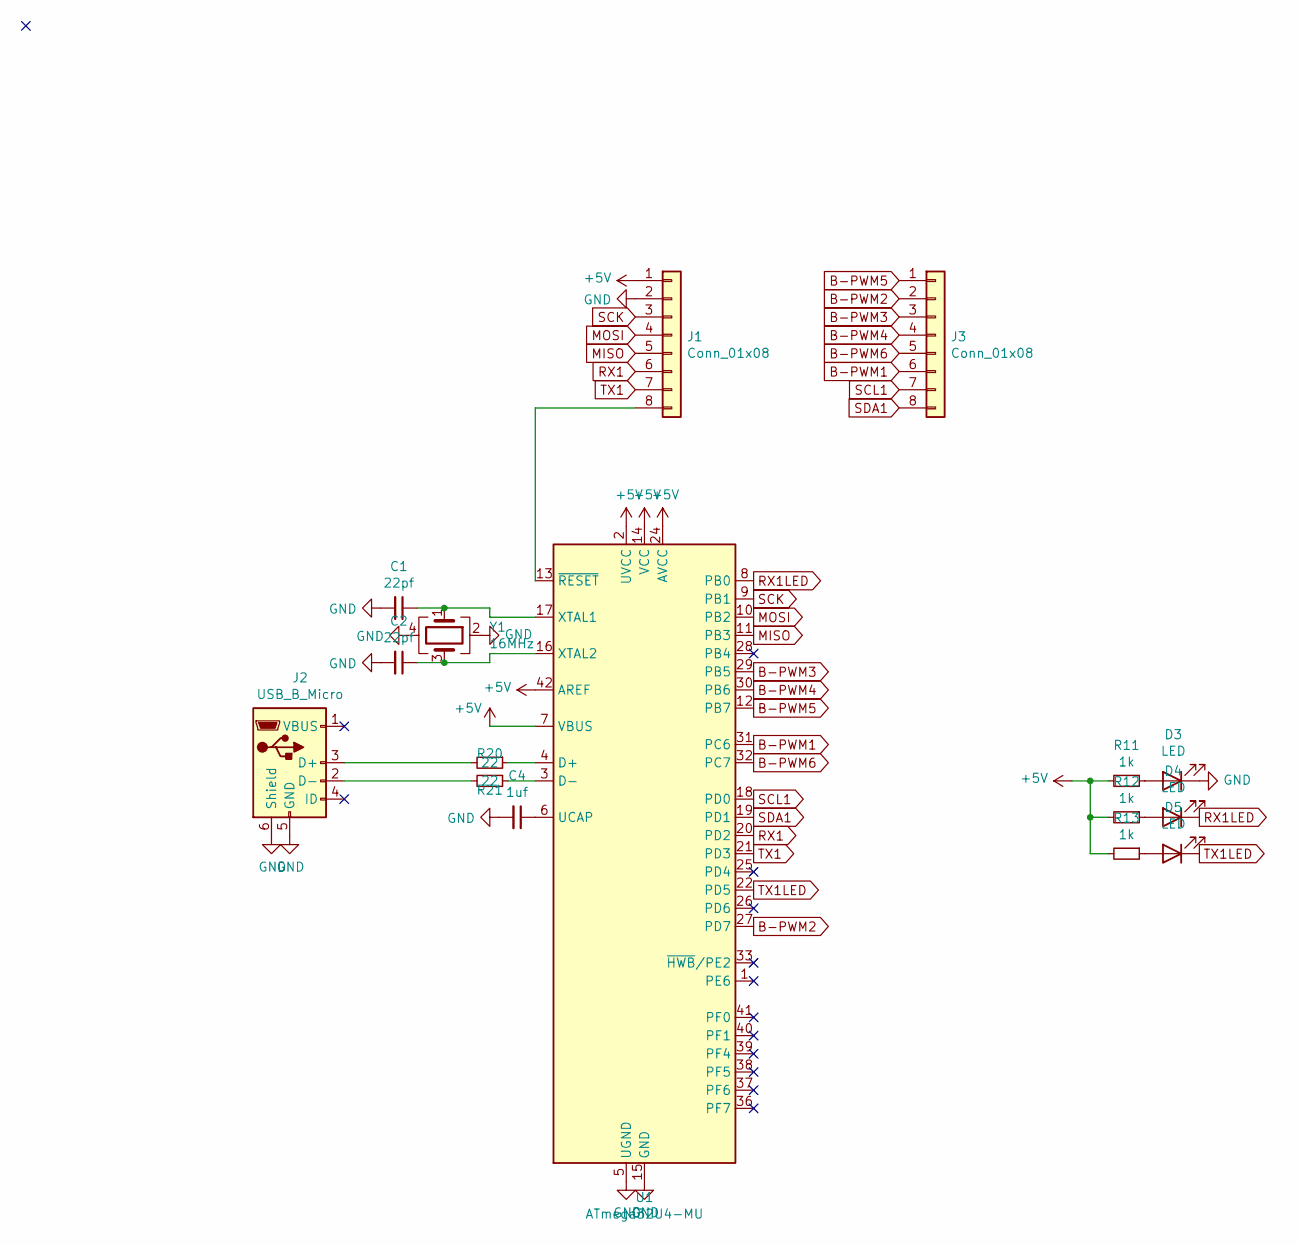
[picture p173: schematic main.kicad_sch]

Parts:
C1, C2: 22pf; C_0402_1005Metric; LCSC C1555
C4: 1uf; C_0402_1005Metric; LCSC C52923
D3, D4, D5: LED; LED_0402_1005Metric; LCSC C130725
J1, J3: Conn_01x08; PinHeader_1x08_P2.54mm_Vertical
J2: USB_B_Micro; USB_Micro-B_Molex_47346-0001; LCSC C132560
R11, R12, R13: 1k; R_0402_1005Metric; LCSC C11702
R20, R21: 22; R_0402_1005Metric; LCSC C25092
U1: ATmega32U4-MU; QFN-44-1EP_7x7mm_P0.5mm_EP5.2x5.2mm; LCSC C112161
Y1: 16MHz; Crystal_SMD_3225-4Pin_3.2x2.5mm; LCSC C164049

Connections:
+5V: J1.1, R11.2, R12.2, R13.2, U1.2 (UVCC), U1.7 (VBUS), U1.14 (VCC), U1.24 (AVCC), U1.34 (VCC), U1.42 (AREF), U1.44 (AVCC)
B-PWM1: J3.6, U1.31 (PC6)
B-PWM2: J3.2, U1.27 (PD7)
B-PWM3: J3.3, U1.29 (PB5)
B-PWM4: J3.4, U1.30 (PB6)
B-PWM5: J3.1, U1.12 (PB7)
B-PWM6: J3.5, U1.32 (PC7)
GND: C1.2, C2.2, C4.2, D3.1 (K), J1.2, J2.5 (GND), J2.6 (Shield), U1.5 (UGND), U1.15 (GND), U1.23 (GND), U1.35 (GND), U1.43 (GND), U1.45 (GND), Y1.2, Y1.4
MISO: J1.5, U1.11 (PB3)
MOSI: J1.4, U1.10 (PB2)
unnamed: C1.1, U1.17 (XTAL1), Y1.1
unnamed: C2.1, U1.16 (XTAL2), Y1.3
unnamed: C4.1, U1.6 (UCAP)
unnamed: D3.2 (A), R11.1
unnamed: D4.2 (A), R12.1
unnamed: D5.2 (A), R13.1
unnamed: J1.8, U1.13 (~RESET)
unnamed: J2.2 (D-), R21.2
unnamed: J2.3 (D+), R20.2
unnamed: R20.1, U1.4 (D+)
unnamed: R21.1, U1.3 (D-)
RX1: J1.6, U1.20 (PD2)
RX1LED: D4.1 (K), U1.8 (PB0)
SCK: J1.3, U1.9 (PB1)
SCL1: J3.7, U1.18 (PD0)
SDA1: J3.8, U1.19 (PD1)
TX1: J1.7, U1.21 (PD3)
TX1LED: D5.1 (K), U1.22 (PD5)

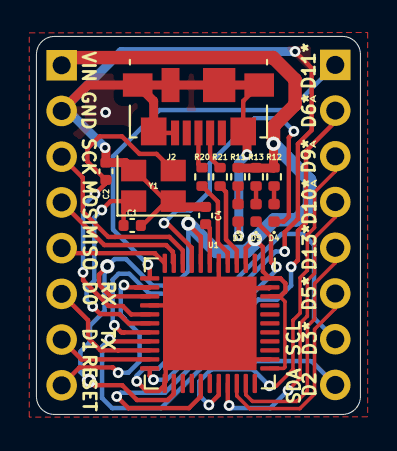
[picture p174: board main.kicad_pcb from above]

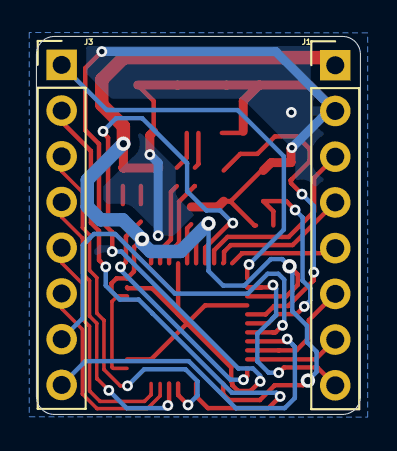
[picture p175: board main.kicad_pcb from below]

Board: 2 copper layers, 18.0 x 21.0 mm, 16 parts (2 on the bottom side), 28 nets.
