MUNAKATA-EPC/Artemis_2023/KiCad_Projects/2022 late/TJ3B_ver/psu_board/psu_board/psu_board.kicad_pcb

## KiCad design KiCad_Projects/2022 late/TJ3B_ver/psu_board/psu_board/psu_board.kicad_pcb (2022-07-10, an earlier design)

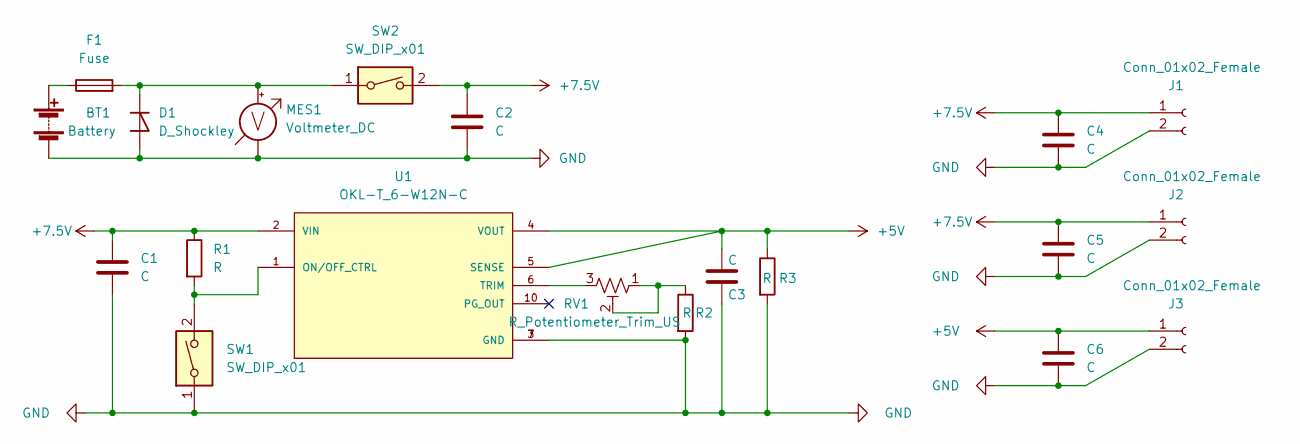
[picture p176: schematic psu_board.kicad_sch]

Parts:
BT1: Battery; JST_VH_B2P-VH-B_1x02_P3.96mm_Vertical
C1, C3, C6: C; C_Disc_D3.8mm_W2.6mm_P2.50mm
C2, C4, C5: C; CP_Radial_D5.0mm_P2.50mm
D1: D_Shockley; D_5W_P10.16mm_Horizontal
F1: Fuse; fuse_socket
J1, J2, J3: Conn_01x02_Female; JST_XH_B2B-XH-A_1x02_P2.50mm_Vertical
MES1: Voltmeter_DC; voltage_counter
R1, R2, R3: R; R_Axial_DIN0204_L3.6mm_D1.6mm_P5.08mm_Horizontal
RV1: R_Potentiometer_Trim_US; Potentiometer_Bourns_3296W_Vertical
SW1: SW_DIP_x01; 2MS1T2B4M2QES
SW2: SW_DIP_x01; DS-850k
U1: OKL-T_6-W12N-C; DCDC-murata-6A

Connections:
+5V: C3.1, C6.1, J3.1, R3.1, U1.4 (VOUT), U1.5 (SENSE)
+7.5V: C1.1, C2.1, C4.1, C5.1, J1.1, J2.1, R1.1, SW2.2, U1.2 (VIN)
GND: BT1.2 (-), C1.2, C2.2, C3.2, C4.2, C5.2, C6.2, D1.2 (A), J1.2, J2.2, J3.2, MES1.1 (-), R2.2, R3.2, SW1.1, U1.3 (GND), U1.7 (GND)
unnamed: BT1.1 (+), F1.1
unnamed: D1.1 (K), F1.2, MES1.2 (+), SW2.1
unnamed: R1.2, SW1.2, U1.1 (ON/OFF_CTRL)
unnamed: R2.1, RV1.1, RV1.2
unnamed: RV1.3, U1.6 (TRIM)

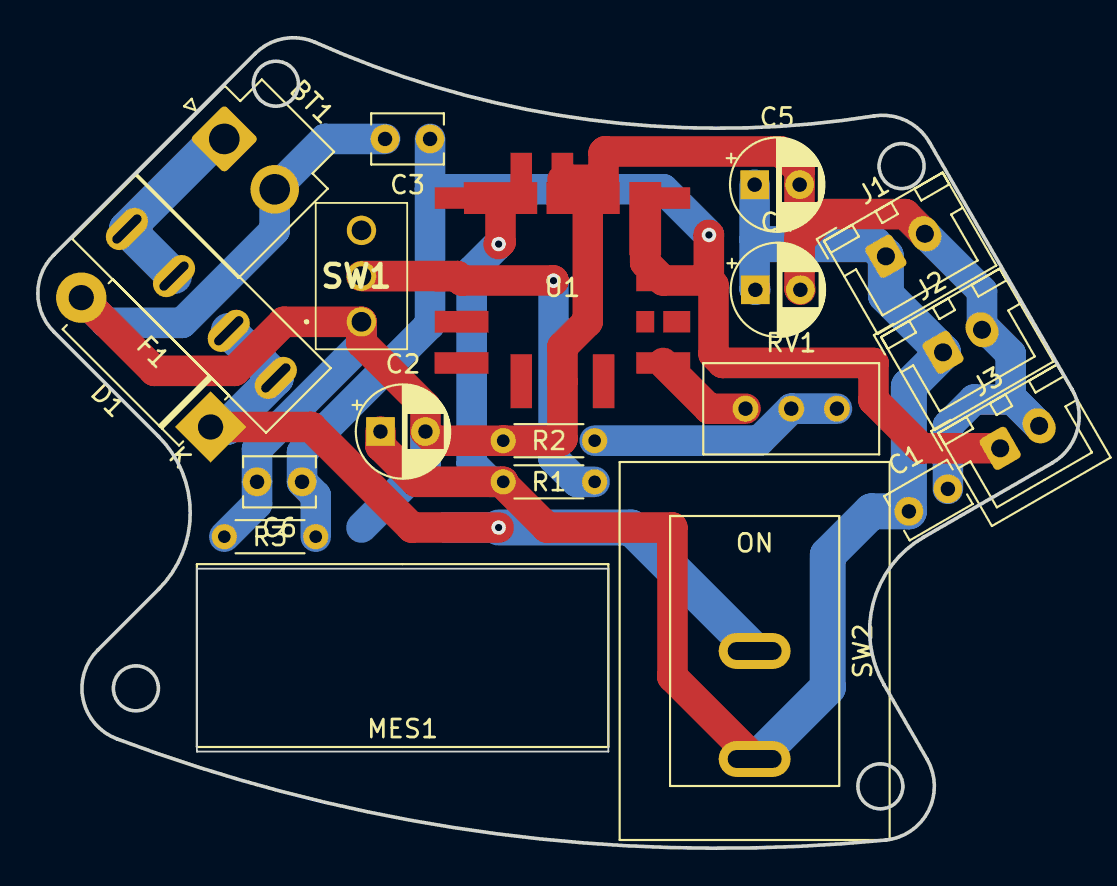
[picture p177: board KiCad_Projects/2022 late/TJ3B_ver/psu_board/psu_board/psu_board.kicad… from above]

Board: 2 copper layers, 57.9 x 45.0 mm, 20 parts (0 on the bottom side), 8 nets.
