MUNAKATA-EPC/Artemis_2023/KiCad_Projects/2022 early/main_board/main board old/main board.kicad_pcb

## KiCad design KiCad_Projects/2022 early/main_board/main board old/main board.kicad_pcb (2022-07-11, an earlier design)

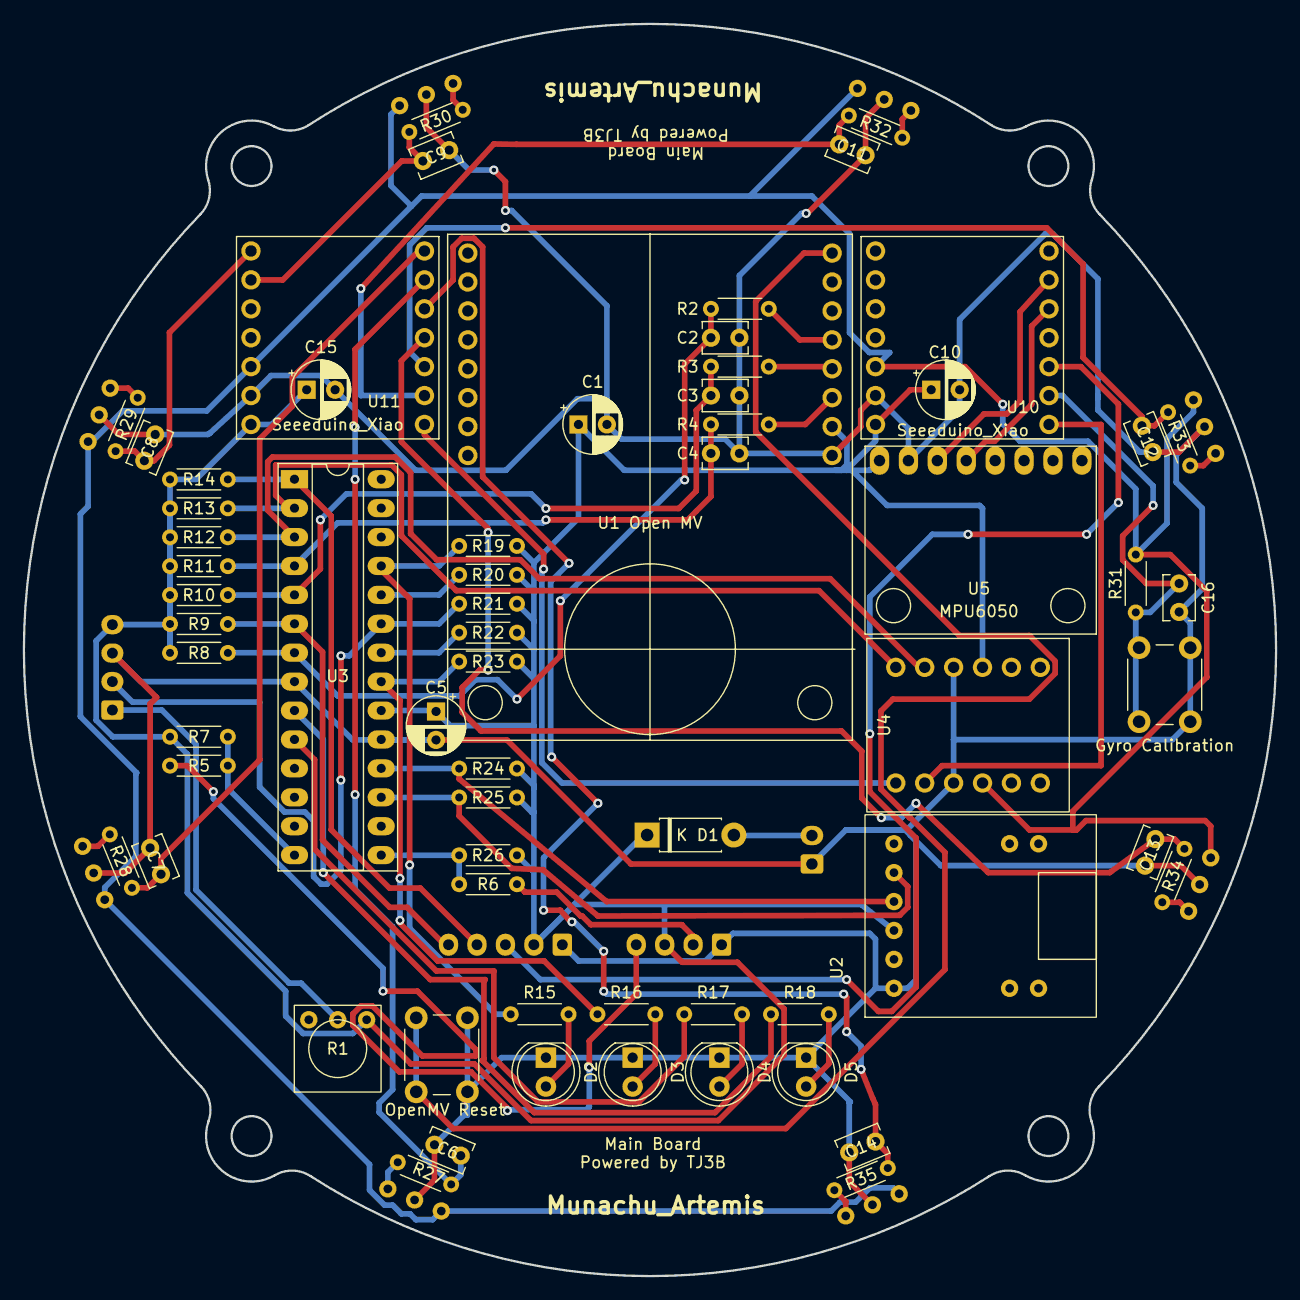
[picture p178: board main board.kicad_pcb from above]

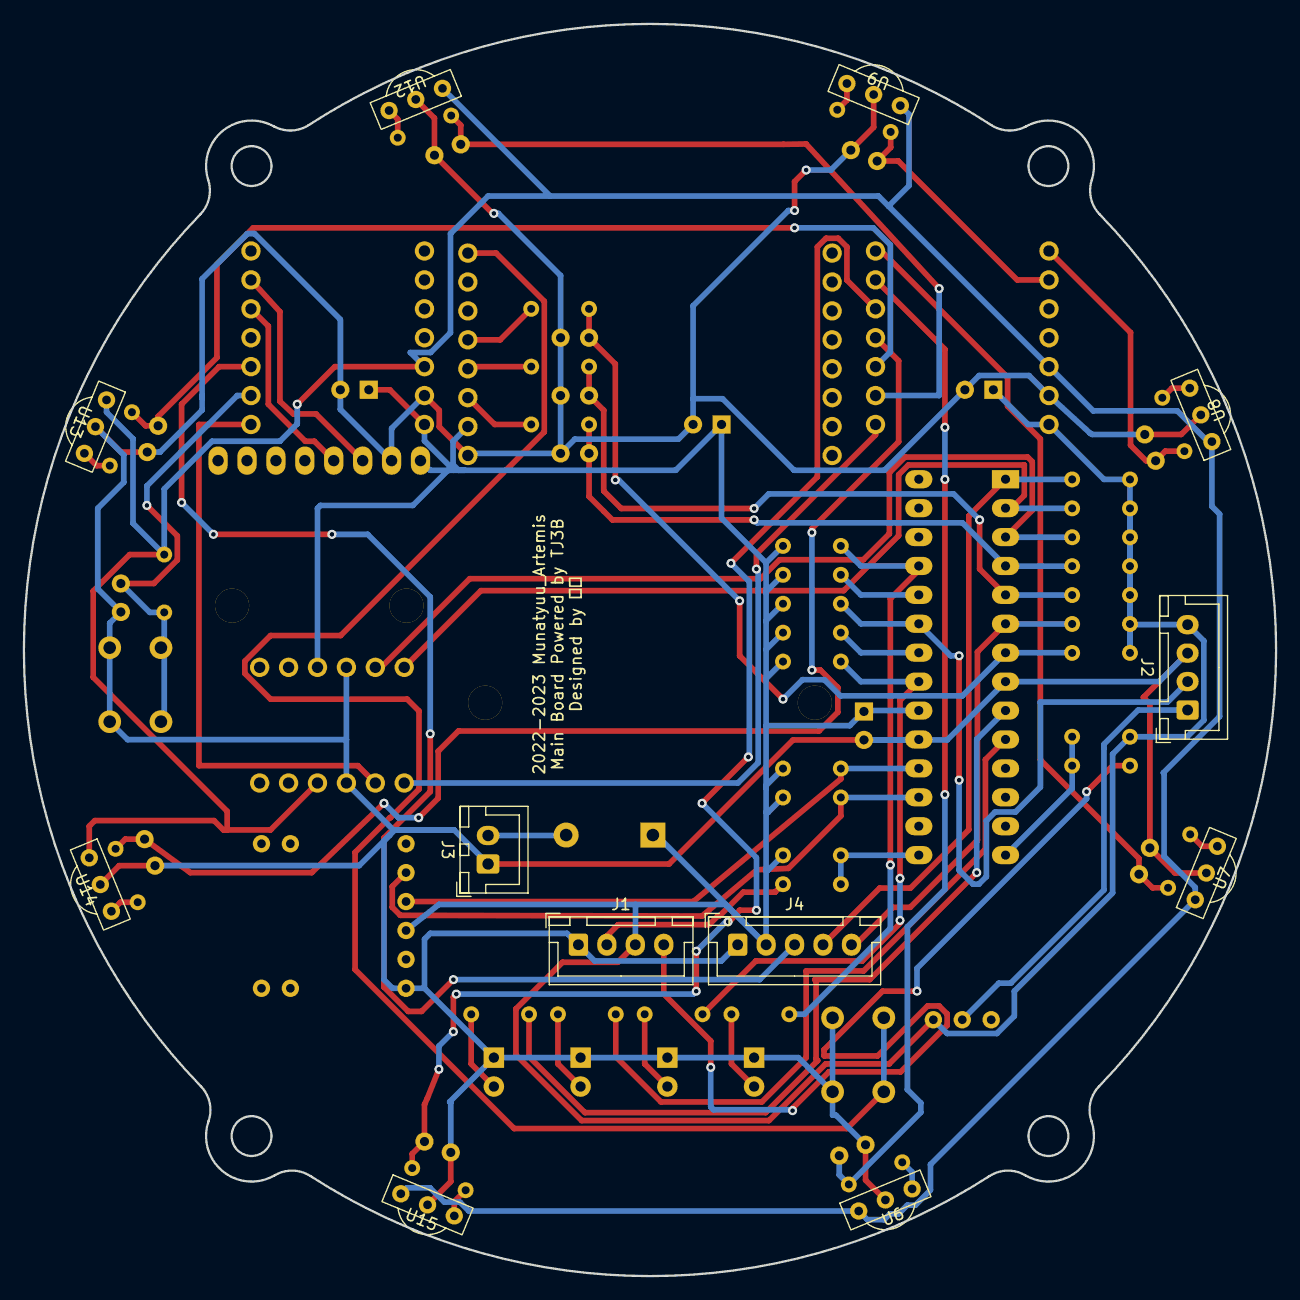
[picture p179: board main board.kicad_pcb from below]

Board: 2 copper layers, 110.0 x 110.0 mm, 77 parts (12 on the bottom side), 55 nets.

Parts:
C1, C5, C10, C15: C; CP_Radial_D5.0mm_P2.50mm
C2, C3, C4, C6, C7, C8, C9, C11, C12, C13, C14, C16: C_Small; C_Disc_D3.8mm_W2.6mm_P2.50mm
D1: D; D_DO-41_SOD81_P7.62mm_Horizontal
D2, D3, D4, D5: LED; LED_D5.0mm_Clear
Gyro Calibration: SW_Push; SW_PUSH_6mm_H5mm
J1, J2: Conn_01x04_Female; JST_XH_B4B-XH-A_1x04_P2.50mm_Vertical
J3: Conn_01x02_Female; JST_XH_B2B-XH-A_1x02_P2.50mm_Vertical
J4: Conn_01x05_Female; JST_XH_B5B-XH-A_1x05_P2.50mm_Vertical
OpenMV Reset: SW_Push; SW_PUSH_6mm_H5mm
R1: R_Variable; R_Varlable
R2, R3, R4, R31: R; R_Axial_DIN0204_L3.6mm_D1.6mm_P5.08mm_Horizontal
R5, R6, R7, R9, R14, R24, R25, R26: 10k; R_Axial_DIN0204_L3.6mm_D1.6mm_P5.08mm_Horizontal
R8, R10, R11, R12, R13, R19, R20, R21, R22, R23, R27, R28, R29, R30, R32, R33, R34, R35: 100k; R_Axial_DIN0204_L3.6mm_D1.6mm_P5.08mm_Horizontal
R15, R16, R17, R18: 330; R_Axial_DIN0204_L3.6mm_D1.6mm_P5.08mm_Horizontal
U1 Open MV: open_mv; OpenMV
U2: type-c_sirial; Type-C_Sirial_Board
U3: PIC18F26K20_ISS; DIP-28_W7.62mm_Socket_LongPads
U4: Akizuki_Logiv_Level_converter; Akizuki_Logic_Level_converter
U5: MPU6050
U6, U7, U8, U9, U12, U13, U14, U15: TSSP58038; TSSP58038_IR
U10, U11: Seeeduino_Xiao; seeeduinoXIAO

Connections:
+3V3: R31.1, U4.9 (LV), U6.2 (Vin), U7.2 (Vin), U8.2 (Vin), U9.2 (Vin), U10.12 (3V3), U11.12 (3V3), U12.2 (Vin), U13.2 (Vin), U14.2 (Vin), U15.2 (Vin)
+5V: C1.1, C5.1, C10.1, C15.1, D1.1 (K), J1.3, J2.4, J4.2, R1.1, R7.1, R8.1, R9.1, R10.1, R11.1, R12.1, R13.1, R14.1, R19.1, R20.1, R21.1, R22.1, R23.1, R24.1, R25.1, R26.1, U1 Open MV.10 (vin), U2.3 (VCC), U3.20 (Vdd), U4.4 (HV), U5.1 (VCC), U10.14 (5V), U11.14 (5V)
AD1: R13.2, U3.2 (RA0/AN0), U4.1 (HV1)
AD2: R12.2, U3.3 (RA1/AN1), U4.2 (HV2)
AD3: C4.1, R4.2, R11.2, U3.4 (RA2/Vref-AN2)
AD4: C3.1, R3.2, R10.2, U3.5 (RA3/Vref+AN3)
AD5: C2.1, R2.2, R8.2, U3.7 (RA5/AN4)
AD6: J2.2, R21.2, U3.23 (AN8/INT2/RB2)
AD7: R20.2, U3.24 (AN9/RB3)
AD8: R22.2, U3.22 (AN10/INT1/RB1)
AD9: R15.1, R19.2, U3.25 (AN11/RB4)
AD10: R16.1, R23.2, U3.21 (AN12/INT0/RB0)
GND: C1.2, C2.2, C3.2, C4.2, C5.2, C6.1, C7.1, C8.1, C9.1, C10.2, C11.2, C12.2, C13.2, C14.2, C15.2, C16.2, D2.1 (K), D3.1 (K), D4.1 (K), D5.1 (K), Gyro Calibration.2, J1.1, J2.3, J3.1, J4.1, OpenMV Reset.2, U1 Open MV.9 (gnd), U2.1 (GND), U3.8 (Vss), U3.19 (Vss), U4.3 (GND), U4.10 (GND), U5.2 (GND), U6.1 (GND), U7.1 (GND), U8.1 (GND), U9.1 (GND), U10.13 (GND), U11.13 (GND), U12.1 (GND), U13.1 (GND), U14.1 (GND), U15.1 (GND)
IR1: C11.1, R32.1, U11.2
IR2: C12.1, R33.1, U11.3
IR3: C13.1, R34.1, U11.4
IR4: C14.1, R35.1, U11.5 (SDA)
IR5: C6.2, R27.2, U11.6 (SCL)
IR6: C7.2, R28.2, U11.7 (TX)
IR7: C8.2, R29.2, U11.8 (RX)
IR8: C9.2, R30.2, U11.9 (SCK)
LV1: U4.12 (LV1), U11.1 (DAC)
LV2: U4.11 (LV2), U10.1 (DAC)
MCLR: J4.4, R14.2, U3.1 (~MCLR/RE3)
MON LED: R17.1, U3.10 (RA6/OSC2/CLKOUT)
unnamed: D1.2 (A), J3.2
unnamed: D2.2 (A), R15.2
unnamed: D3.2 (A), R16.2
unnamed: D4.2 (A), R17.2
unnamed: D5.2 (A), R18.2
unnamed: J1.2, R6.1
unnamed: J1.4, R5.1
unnamed: J2.1, R1.2
unnamed: R2.1, U1 Open MV.13 (seru03)
unnamed: R3.1, U1 Open MV.12 (seru02)
unnamed: R4.1, U1 Open MV.11 (seru01)
unnamed: OpenMV Reset.1, U1 Open MV.16 (rst)
unnamed: R27.1, U6.0 (OUT)
unnamed: R28.1, U7.0 (OUT)
unnamed: R29.1, U8.0 (OUT)
unnamed: R30.1, U9.0 (OUT)
unnamed: U5.4 (SDA), U10.5 (SDA)
unnamed: U5.3 (SCL), U10.6 (SCL)
unnamed: R32.2, U12.0 (OUT)
unnamed: R33.2, U13.0 (OUT)
unnamed: R34.2, U14.0 (OUT)
unnamed: R35.2, U15.0 (OUT)
PWR LED: R18.1, U3.9 (RA7/OSC1/CLKIN)
RA4: J4.5, R9.2, U3.6 (RA4)
RES: C16.1, Gyro Calibration.1, R31.2, U10.2
RX: R24.2, U2.4 (TXD), U3.18 (RX/RC7)
SCL: R5.2, R7.2, U3.14 (SCL/SCK/RC3)
SDA: R6.2, R26.2, U3.15 (SDA/SDI/RC4)
SW2: J4.3, U10.3
TX: R25.2, U2.5 (RXD), U3.17 (TX/RC6)
