MUNAKATA-EPC/Artemis_2023/KiCad_Projects/2022 early/io board/io_board for cnc/io_board for cnc.kicad_sch

## KiCad design KiCad_Projects/2022 early/io board/io_board for cnc/io_board for cnc.kicad_sch (2022-07-31)

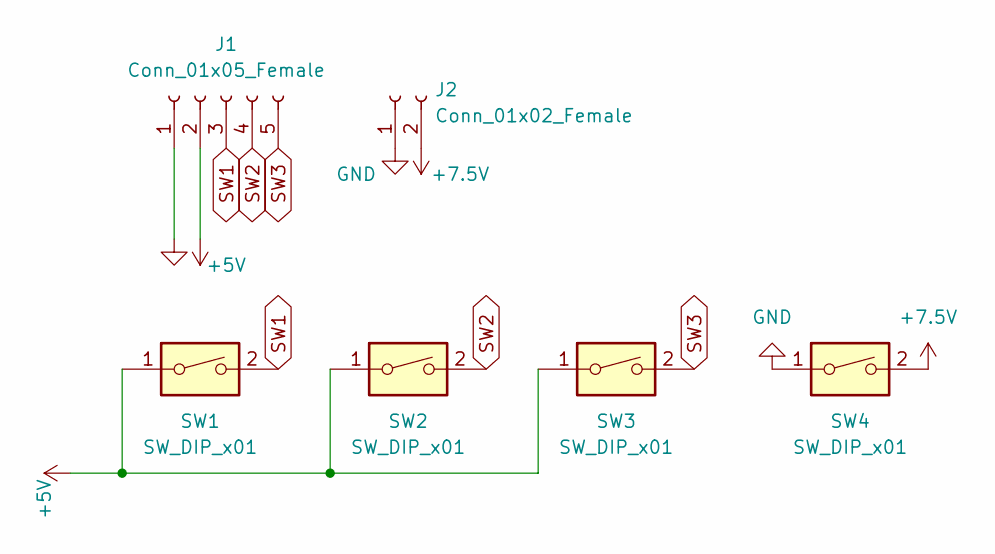
[picture p180: schematic io_board for cnc.kicad_sch]

Parts:
J1: Conn_01x05_Female; JST_XH_B5B-XH-A_1x05_P2.50mm_Vertical
J2: Conn_01x02_Female; JST_XH_B2B-XH-A_1x02_P2.50mm_Vertical
SW1, SW2, SW3: SW_DIP_x01; SW_PUSH_6mm_H5mm
SW4: SW_DIP_x01; DS-850k

Connections:
+5V: J1.2, SW1.1, SW2.1, SW3.1
+7.5V: J2.2, SW4.2
GND: J2.1, SW4.1
SW1: J1.3, SW1.2
SW2: J1.4, SW2.2
SW3: J1.5, SW3.2
