MUNAKATA-EPC/Artemis_2023/KiCad_Projects/2022 early/io board/io_board/io_board.kicad_sch

## KiCad design KiCad_Projects/2022 early/io board/io_board/io_board.kicad_sch (2022-07-28)

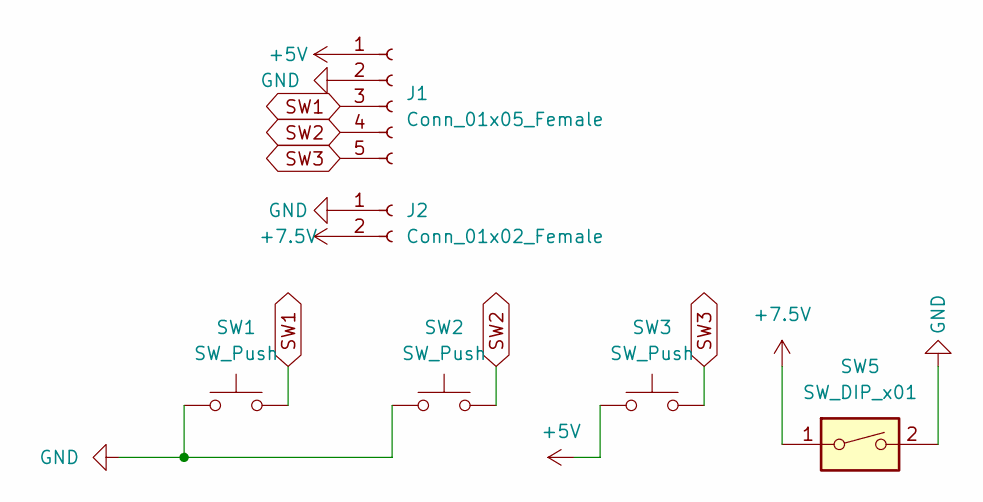
[picture p181: schematic io_board.kicad_sch]

Parts:
J1: Conn_01x05_Female
J2: Conn_01x02_Female; PinSocket_1x02_P2.54mm_Vertical
SW1, SW2, SW3: SW_Push; SW_PUSH_6mm
SW5: SW_DIP_x01; DS-850k

Connections:
+5V: J1.1, SW3.1
+7.5V: J2.2, SW5.1
GND: J1.2, J2.1, SW1.1, SW2.1, SW5.2
SW1: J1.3, SW1.2
SW2: J1.4, SW2.2
SW3: J1.5, SW3.2
