MUNAKATA-EPC/Artemis_2023/Program/main/Teeensy/Artemis_Robo_Teensy40/include/debug_program.h

namespace PID_PROG
{
    float gains_gyro[3] = {0.60, 0, 2};
    
    void Main_Program()
    {
        PID_loop(Gyro_Deg / 2, gains_gyro);

        Move(0, 0);
    }
}

namespace LINE_PROG
{
    float gains_gyro[3] = {0.60, 0, 2};

    void Main_Program()
    {
        PID_loop(Gyro_Deg / 2, gains_gyro);

        if(Line_Value == -1)
        {
            Move(0, 0);
        }
    }
}

namespace DEBUG_PROG
{
    void Main_Program(int debug)
    {
        Move(0, 20);
    }
}
