MUNAKATA-EPC/Artemis_2023/Tournaments/2023_00_KitakyusyuOpen/Program/goal and gyro pid/NewFile-00.c

//--------------------------------------------------------------------------------
// Title: Main - [ NewFile-00 ]
// Build:DAISEN C-Style for TJ3B  [ Ver.20190706 ] - [ Build_V190617 ]
//--------------------------------------------------------------------------------
// SetupVal:111111-110010-000002,cmt:
// CN01:Ball
// CN02:Line
// CN03:L-Touch
// CN04:R-Touch
// CN05:C-Touch
// CN06:
// CN07:
// CN08:
// CN09:RED3
// CN10:RED2
//--------------------------------------------------------------------------------
#include "D_Main.h"
#include "D_I2C.h"
#include "D_SIO.h"
#include "D_EIO.h"
//--------------------------------------------------------------------------------
// Program Name : NewFile-00.C
//--------------------------------------------------------------------------------
void user_main(void)
{
  while (TRUE) {
    gPwm[0] = 0x1E;
    gPwm[1] = 0x1E;
    gPwm[2] = 0x1E;
    gPwm[3] = 0x1E;
    pwm_out();
  }
}
//--------------------------------------------------------------------------------
